tunasafa/mp3-player-enclosure/touchscreen_metal/design_overview.pdf

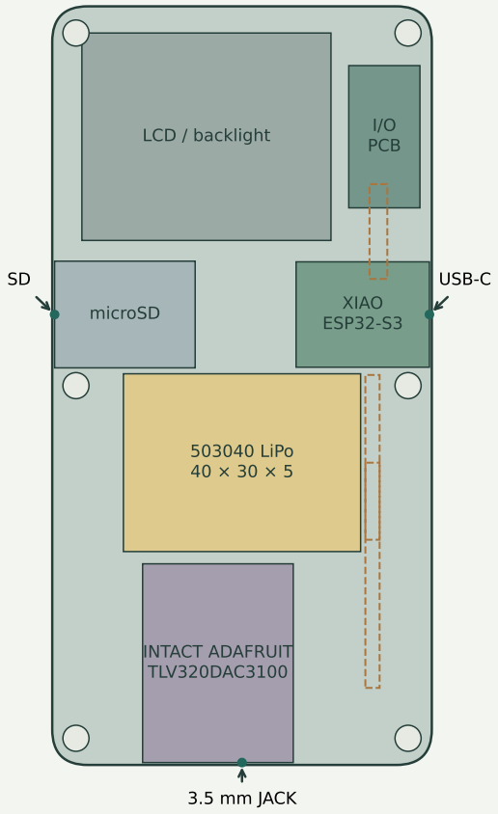
[picture p4: figure]
LCD / backlight; PCB; XIAO ESP32-S3 microSD; 503040 LiPo 40 × 30 × 5; INTACT ADAFRUIT TLV320DAC3100; USB-C; 3.5 mm JACK

LANDSCAPE
296 × 240

## mytunas

64 mm

128 mm

43 × 36 mm outer glass

### 01 / METAL FRONT

### 02 / PACKING — front-coordinate plan

# 8.3 mm aggressive prototype

0.4 mm steel front / 0.15 mm insulation 7.1 mm full Adafruit product height

0.18 mm clearance + 0.07 mm liner

0.4 mm steel rear

# Separate battery bay

5 mm nominal protected pack

2.13 mm to the rear liner

1.7 mm of that reserved clear

# Port alignment

USB right · SD left · headphones bottom

Actual board transforms set USB/jack axes

Blind pockets retain a 1 mm outer lip

# Strict nominal checks

0 assembly collisions

0 reserved-space collisions

Connected, watertight shell / carrier meshes

# Physical fit still required

Panel border and side tails estimated
SD assembly and interface PCB provisional

Unsealed ports; no water/dust rating

### 03 / THICKNESS LIMIT

# mytunas / touch

### T03 / BATTERY ABOVE DAC / BOTTOM JACK / 64 × 128 × 8.3 mm

Metal faces + separate frame. Same coordinates as STEP and viewer; dimensions in millimetres.
Not a fabrication release: qualify plate flatness, deflection, insulation, tolerances and physical component fit.
