tunasafa/mp3-player-enclosure/touchscreen_01/design_overview.pdf

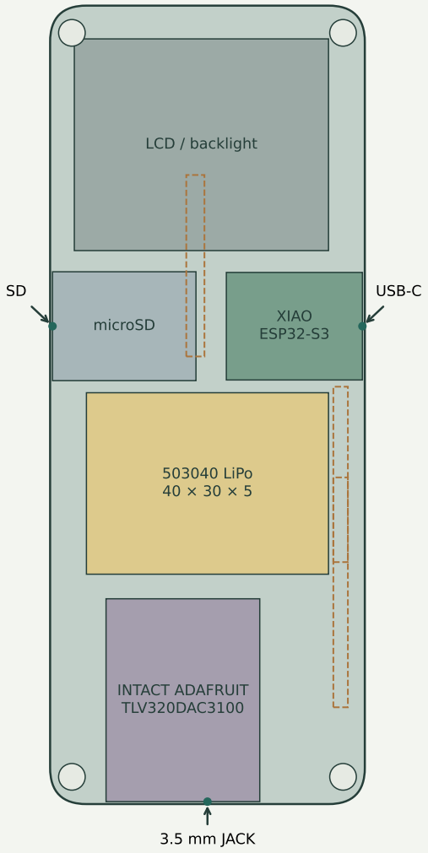
[picture p5: figure]
LCD / backlight; XIAO ESP32-S3 microSD; 503040 LiPo 40 × 30 × 5; INTACT ADAFRUIT TLV320DAC3100; USB-C; 3.5 mm JACK

LANDSCAPE
296 × 240

## mytunas

52 mm

132 mm

43 × 36 mm outer glass

### 01 / FRONT

### 02 / PACKING — front-coordinate plan

# 10.4 mm practical target

1.2 mm front skin
0.6 mm board mounting height

7.1 mm full Adafruit product height

0.3 mm rear clearance

1.2 mm rear skin

# Separate battery bay

5 mm nominal protected pack

2.4 mm to the rear skin

1.7 mm of that reserved clear

# Port alignment

USB right · SD left · headphones bottom

Actual board transforms set USB/jack axes

Blind pockets retain a 1 mm outer lip

# Strict nominal checks

0 assembly collisions

0 reserved-space collisions

Connected, watertight shell / carrier meshes

# Physical fit still required

Panel border and folded ribbons estimated SD assembly and interface PCB provisional

Unsealed ports; no water/dust rating

### 03 / THICKNESS LIMIT

# mytunas / touch

### T02 / BATTERY ABOVE DAC / BOTTOM JACK / 52 × 132 × 10.4 mm

Same parts and coordinates as the STEP assembly and interactive viewer. All dimensions in millimetres. Prototype: sample measurements, flex folding, PCB selection and a physical fit test remain necessary.
