tunasafa/mp3-player-enclosure/revision_04/design_overview.pdf

FRONT SHELL / INSIDE | REAR SHELL / INSIDE

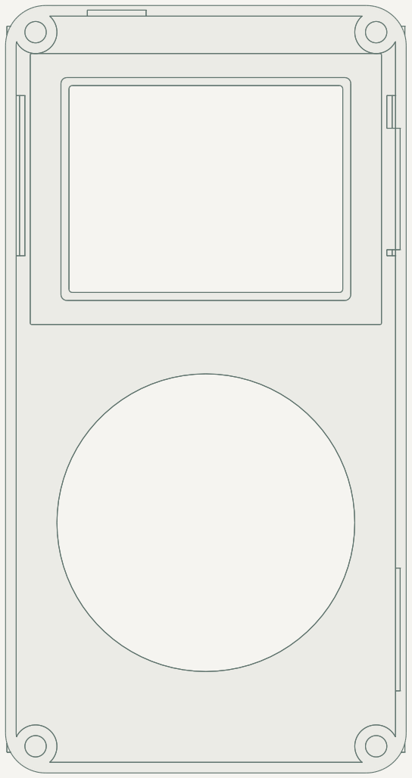
[picture p6: figure]

LCD

Wheel
Battery
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
Assembly Z / mm (front

# → rear)

COMPONENT DEPTH RANGES

# FORM 04 / COMPACT FIT PROTOTYPE

### 115 × 60 × 12.9 mm · repacked with unchanged components · no middle carrier

Lens recess, wheel aperture and local UI pads. Four blind insert bosses; two locating tongues.

Board pads, insertion fences and 503040 battery guides. Viewed through front; same X/Y on both drawings.

Clickwheel adapter to wall: 2.35 mm. Battery to rear skin: 1.7 mm.
DAC to LCD / rear skin: 0.3 / 0.3 mm. These gaps still need real-part verification.

115 x 60 x 12.9 mm; 0.2 mm thinner than 13.1 mm. Battery entirely below LCD; no footprint growth. Flipped upper DAC; 1.0 mm local LCD seat floor.

CAD/mesh checks passed. The component envelopes and connector positions remain provisional.

Print an empty-shell fit set first. Exact wheel/LCD geometry, flex routes, audio mounting and battery sample fit are still required.
