tunasafa/mp3-player-enclosure/touchscreen_02/drawings.pdf

# mytunas / Model 02

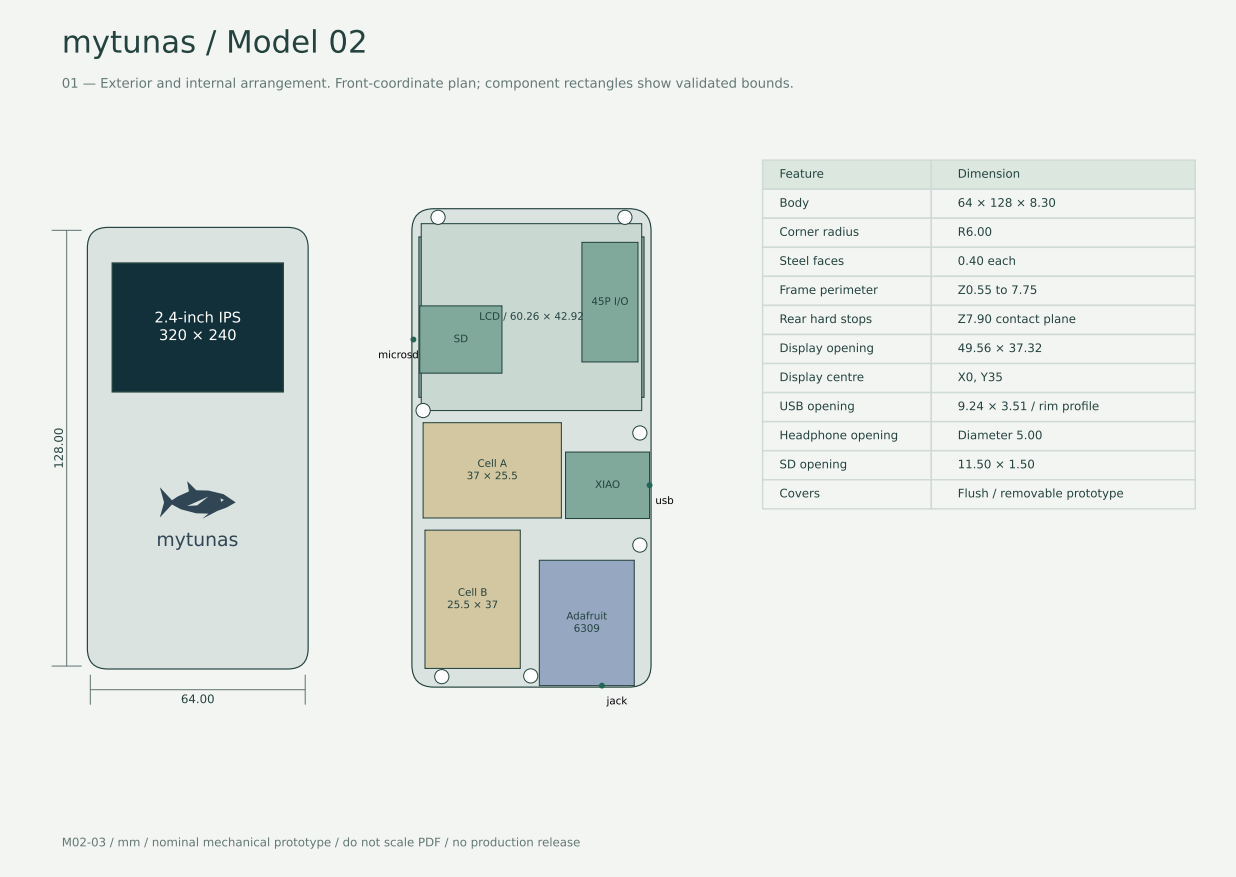
[picture p7: page 1]
2.4-inch IPS 320 × 240; LCD; Cell A 37 × 25.5; Cell B 25.5 × 37; Adafruit 6309; XIAO; usb; jack; microsd; Rear hard stops; Z7.90 contact plane; Headphone opening; Diameter 5.00; SD opening; Covers; Flush / removable prototype

01 — Exterior and internal arrangement. Front-coordinate plan; component rectangles show validated bounds.

Feature | Dimension

Body | 64 × 128 × 8.30

Corner radius | R6.00

Steel faces | 0.40 each

Frame perimeter | Z0.55 to 7.75

Display opening | 49.56 × 37.32

Display centre | X0, Y35

USB opening | 9.24 × 3.51 / rim profile

M02-03 / mm / nominal mechanical prototype / do not scale PDF / no production release

ID | X | Y | Fastener
1 | -25.00 | 61.70 | M1.6 × 5 / CSK

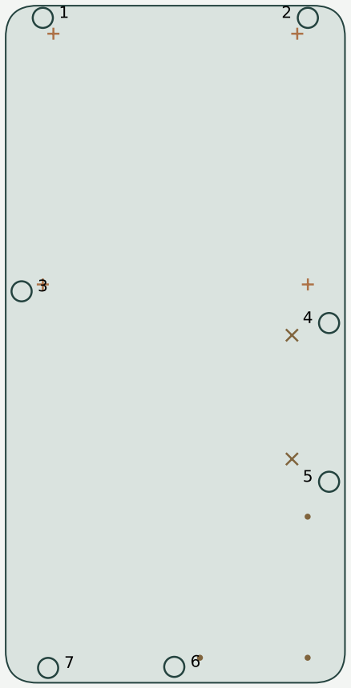
[picture p8: figure]

2 | 25.00 | 61.70 | M1.6 × 5 / CSK
3 | -29.00 | 10.00 | M1.6 × 5 / CSK
4 | 29.00 | 4.00 | M1.6 × 5 / CSK
5 | 29.00 | -26.00 | M1.6 × 5 / CSK
6 | -0.20 | -61.00 | M1.6 × 5 / CSK
7 | -24.00 | -61.20 | M1.6 × 5 / CSK
C1 | -25.00 | 11.30 | M1.4 × 3 / carrier
C2 | 25.00 | 11.30 | M1.4 × 3 / carrier
C3 | -23.00 | 58.70 | M1.4 × 3 / carrier
C4 | 23.00 | 58.70 | M1.4 × 3 / carrier
X1 | 22.00 | -21.70 | M1.4 × 3 / saddle
X2 | 22.00 | 1.70 | M1.4 × 3 / saddle
D1 | 24.96 | -32.60 | M1.4 × 3 / rear column
D2 | 4.64 | -59.27 | M1.4 × 3 / rear column
D3 | 24.96 | -59.27 | M1.4 × 3 / rear column
Mouth centre | X | Y | Z
usb | 31.6000 | -9.9927 | 3.6050
jack | 18.8592 | -63.6000 | 4.4225
microsd | -31.6000 | 29.0000 | 6.4000

# Hole and port coordinates

02 — Datum: body centre X0/Y0; front exterior Z0. All dimensions in millimetres.

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
### Z / mm

0.00–0.40

Steel

0.40–0.55

Insulation

0.55–7.65

Published DAC max

7.65–7.83

Free 0.18

7.83–7.90

Liner

7.90–8.30

Steel

## DAC

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
### Z / mm

0.00–0.40

Steel

0.40–0.70

Adhesive

0.70–5.90

Pack max 5.20

5.90–7.60

Expansion 1.70

7.60–7.83

Free 0.23

7.83–7.90

Liner

7.90–8.30

Steel

## Battery

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
### Z / mm

0.00–0.40

Bezel

0.40–0.55

Bond

0.55–4.30

Touch + LCD 3.75

4.30–4.35

Cushion

4.35–4.55

Carrier

4.55–4.85

SD adhesive

4.85–7.45

SD max

7.45–7.83

Free 0.38

7.83–7.90

Liner

7.90–8.30

Steel

## LCD + SD

# Depth sections and reserves

03 — Layer values are nominal allocations. Full published DAC height is retained.

Part / check | Specification | Process note
Frame | PA12 / 13 metal threaded inserts | Use BEFORE_HEAT_INSERTS geometry
Front / rear | 0.40 mm satin polished stainless | 0.03 mm original vector engravings
Carrier | 0.20 web / four 0.30 mm welded blades | Weld in flat fixture; inspect distortion
Case threads | 7 × PEM MSIB-M1.6-300 | Pilot 2.15 / depth 3.77 minimum
Internal threads | 6 × PEM MSIB-M1.4-150 | Pilot 2.15 / depth 2.27 minimum
XIAO saddle | 0.40 steel / 0.30 shield cushion | Two M1.4 × 3 screws; qualify shield load
DAC retention | 3 steel columns / insulated seats | Three rear M1.4 × 3 CSK screws
Ports | Actual USB rim + 0.15 radial gap | Positive clearance; optional covers
Release gate | 0.18 mm DAC clearance is tight | Tolerance stack and physical cycle tests

# Manufacturing and assembly checkpoints

04 — STEP defines 3D geometry. DXF profiles are for the named sheet layers only.

Part | W × L × H | Minimum X, Y, Z
case_insert_1 | 2.50 × 2.50 × 3.00 | -26.25, 60.45, 4.50
case_insert_2 | 2.50 × 2.50 × 3.00 | 23.75, 60.45, 4.50
case_insert_3 | 2.50 × 2.50 × 3.00 | -30.25, 8.75, 4.50
case_insert_4 | 2.50 × 2.50 × 3.00 | 27.75, 2.75, 4.50
case_insert_5 | 2.50 × 2.50 × 3.00 | 27.75, -27.25, 4.50
case_insert_6 | 2.50 × 2.50 × 3.00 | -1.45, -62.25, 4.50
case_insert_7 | 2.50 × 2.50 × 3.00 | -25.25, -62.45, 4.50
carrier_insert_1 | 2.50 × 2.50 × 1.50 | -26.25, 10.05, 2.85
carrier_insert_2 | 2.50 × 2.50 × 1.50 | 23.75, 10.05, 2.85
carrier_insert_3 | 2.50 × 2.50 × 1.50 | -24.25, 57.45, 2.85
carrier_insert_4 | 2.50 × 2.50 × 1.50 | 21.75, 57.45, 2.85
xiao_clamp_insert_1 | 2.50 × 2.50 × 1.50 | 20.75, -22.95, 2.80
xiao_clamp_insert_2 | 2.50 × 2.50 × 1.50 | 20.75, 0.45, 2.80
midframe | 64.01 × 128.01 × 7.35 | -32.00, -64.00, 0.55
front_bezel | 64.01 × 128.01 × 0.41 | -32.00, -64.00, -0.00
rear_shell | 64.01 × 128.01 × 0.41 | -32.00, -64.00, 7.90
front_bond | 64.01 × 128.01 × 0.16 | -32.00, -64.00, 0.40
rear_gasket | 64.01 × 128.01 × 0.16 | -32.00, -64.00, 7.75
touch_glass | 59.96 × 42.62 × 1.25 | -29.98, 13.69, 0.55
lcd | 60.26 × 42.92 × 2.50 | -30.13, 13.54, 1.80

# Part measurement schedule

05 — Bounding dimensions and assembly position; holes and contours are defined by STEP.

Part | W × L × H | Minimum X, Y, Z
display_adhesive | 59.66 × 42.32 × 0.15 | -29.83, 13.84, 0.40
display_carrier | 59.00 × 50.00 × 1.45 | -29.50, 10.00, 4.35
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
usb_cover | 0.45 × 12.60 × 6.00 | 31.55, -16.29, 0.60
sd_cover | 0.45 × 13.20 × 2.60 | -32.00, 22.40, 5.10
jack_cover | 6.50 × 0.45 × 6.50 | 15.61, -64.00, 1.17

08 — Bounding dimensions and assembly position; holes and contours are defined by STEP.
