tunasafa/mp3-player-enclosure/revision_04/studies/dac_orientation/comparison.pdf

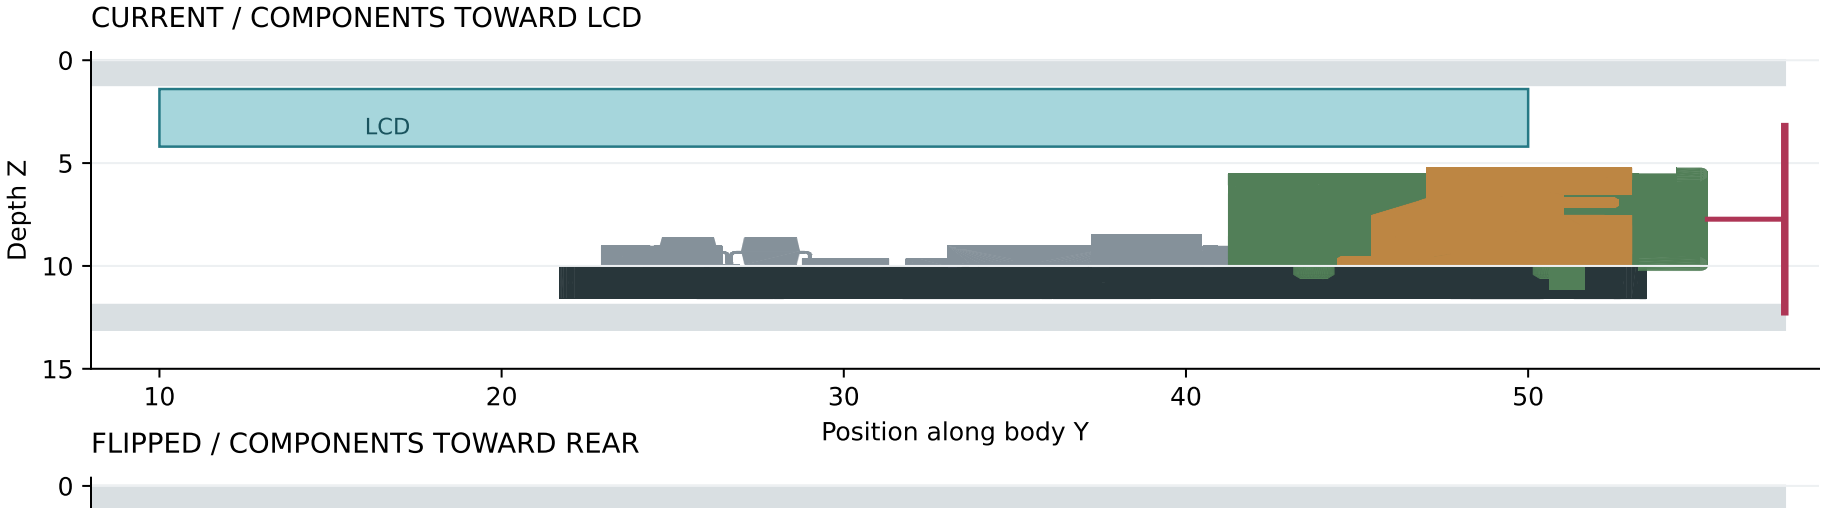
[picture p9: figure]
Position along body Y; Depth Z; LCD; CURRENT / COMPONENTS TOWARD LCD; FLIPPED / COMPONENTS TOWARD REAR

10 | 20 | 30 | 40 | 50
| | Position along body Y

5

10

15

Depth Z

LCD

10 | 20 | 30 | 40 | 50
| | Position along body Y

0

5

10

15

Depth Z

LCD

CONDITIONAL / NOMINAL CAD HEIGHT

# mytunas / DAC orientation study

Same Adafruit 6309 board, including both connectors. Dimensions in mm.

Case: 13.1
Jack axis Z: 7.728

Rear aperture ligament: 0.872

Published board stack: 7.1 Envelope rear gap: 0.3

Existing printable design

Case: 13.1
Jack axis Z: 8.372

Rear aperture ligament: 0.228

Published board stack unchanged

Hole and mounts must move
Rear aperture edge becomes thin

Case: 12.4
Jack axis Z: 7.000

Rear aperture ligament: 0.900 CAD-only fit target

7.1 published height NOT cleared

Battery rear space: 1.0

## WHY SIDEWAYS DOES NOT AUTOMATICALLY SAVE DEPTH

Jack housing reaches 14.0 into the board. Free space beside the centered LCD is only 2.4.

The jack and speaker socket still sit over the LCD when rotated to a side port.

Moving them entirely beyond the LCD trades thickness for a larger face footprint.

Side projections of manufacturer CAD, not cross-sections. Gray: shells. Cyan: LCD. Green: jack. Ochre: speaker socket.

Study only: nominal CAD is not a maximum-part drawing. No new print release or electrical qualification.
