tunasafa/mp3-player-enclosure/touchscreen_01/designs/T01_concept/README_SUPERSEDED.md

# Superseded — do not print

These T01 files contain known component and support intersections. The old validation bypass was removed. They are retained only as historical output.

Use the current [T02 bottom-jack exports](../T02_bottom_jack/) and [validated interactive preview](../../preview.html).
