tunasafa/mp3-player-enclosure/revision_04/internal_layout.png

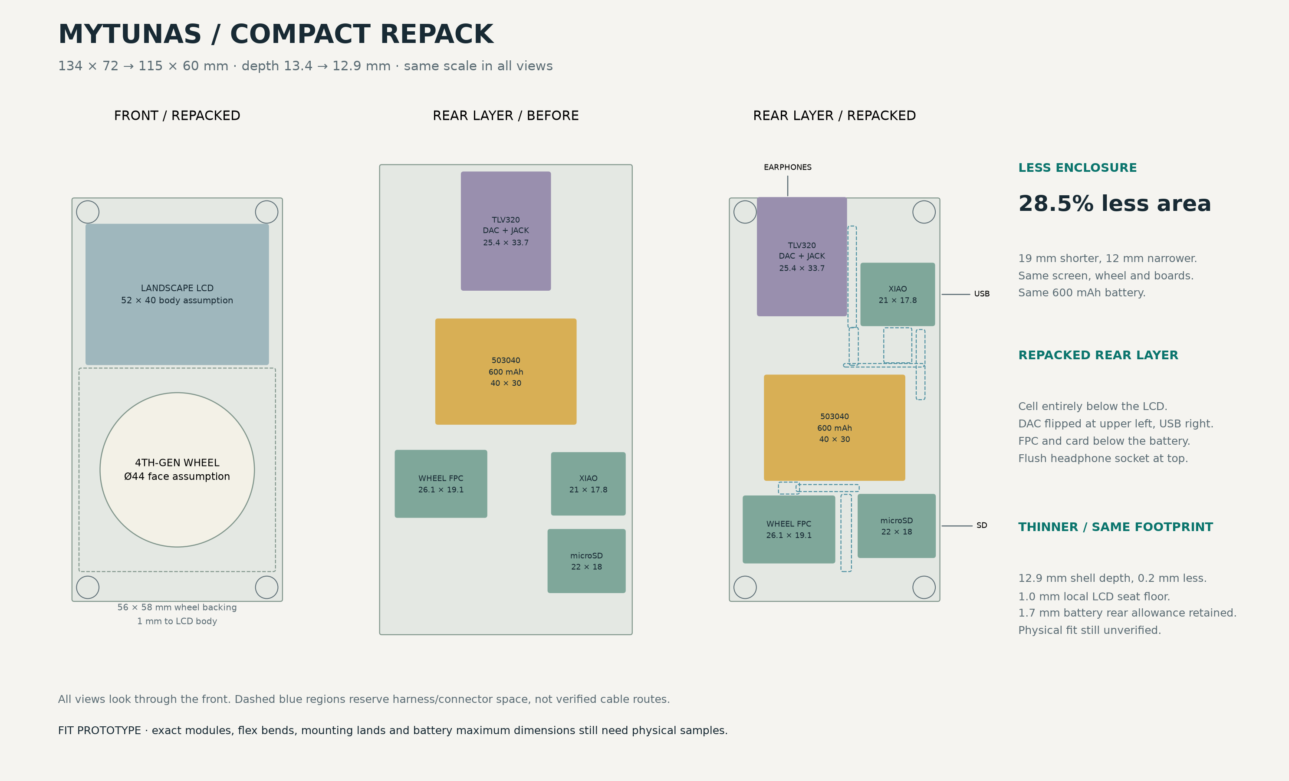
revision_04/internal_layout.png
