tunasafa/mp3-player-enclosure/revision_04/preview_bottom_check.png

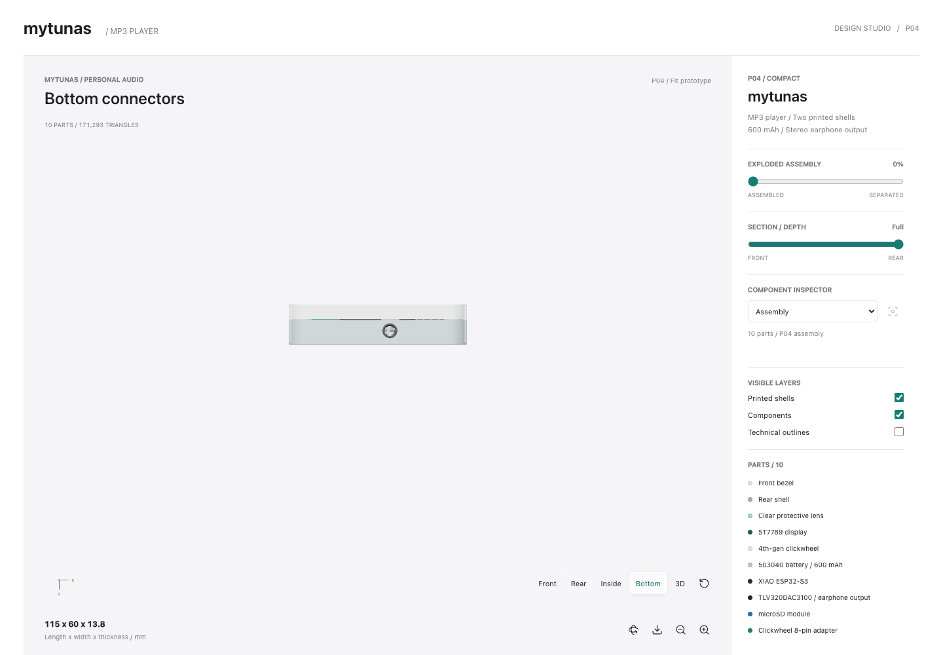
revision_04/preview_bottom_check.png
