tunasafa/mp3-player-enclosure/revision_04/preview_mobile_inside_check.png

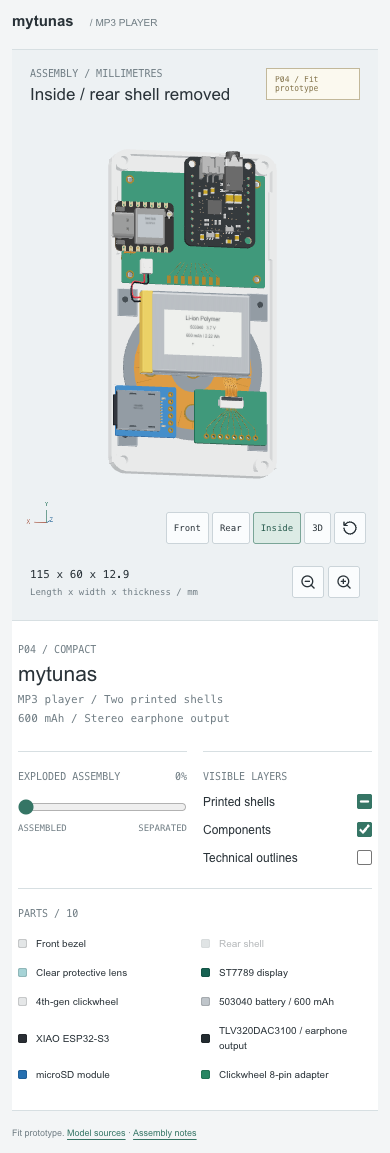
revision_04/preview_mobile_inside_check.png
