tunasafa/mp3-player-enclosure/revision_04/preview_section_check.png

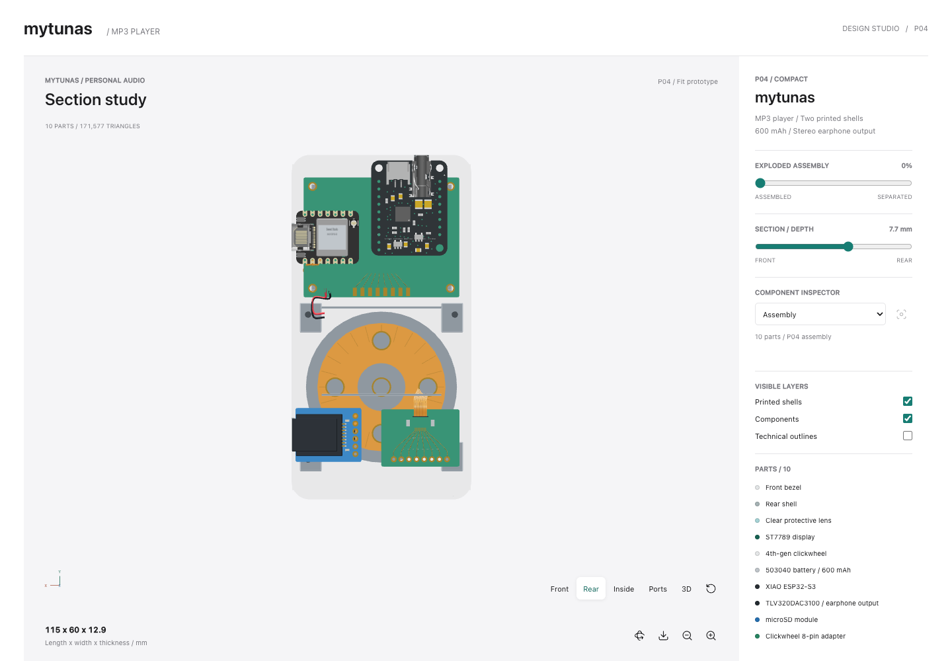
revision_04/preview_section_check.png
