tunasafa/mp3-player-enclosure/revision_04/preview_small_mobile_rear_check.png

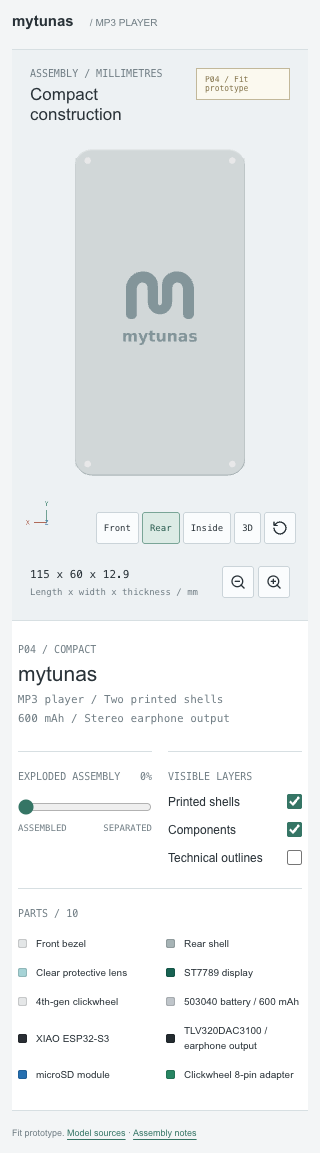
revision_04/preview_small_mobile_rear_check.png
