tunasafa/mp3-player-enclosure/touchscreen_01/design_overview.png

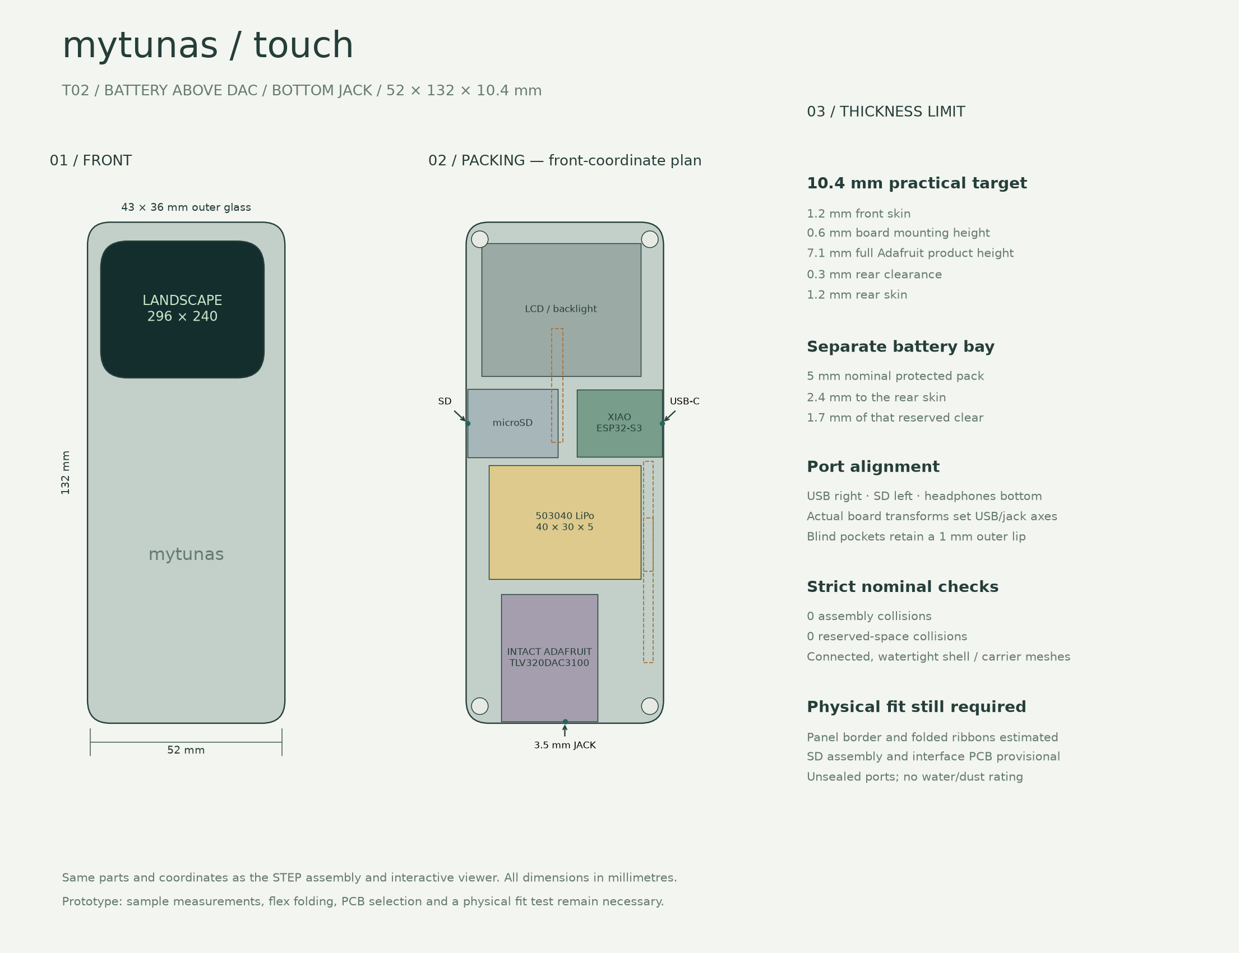
touchscreen_01/design_overview.png
