tunasafa/mp3-player-enclosure/touchscreen_01/preview_back.png

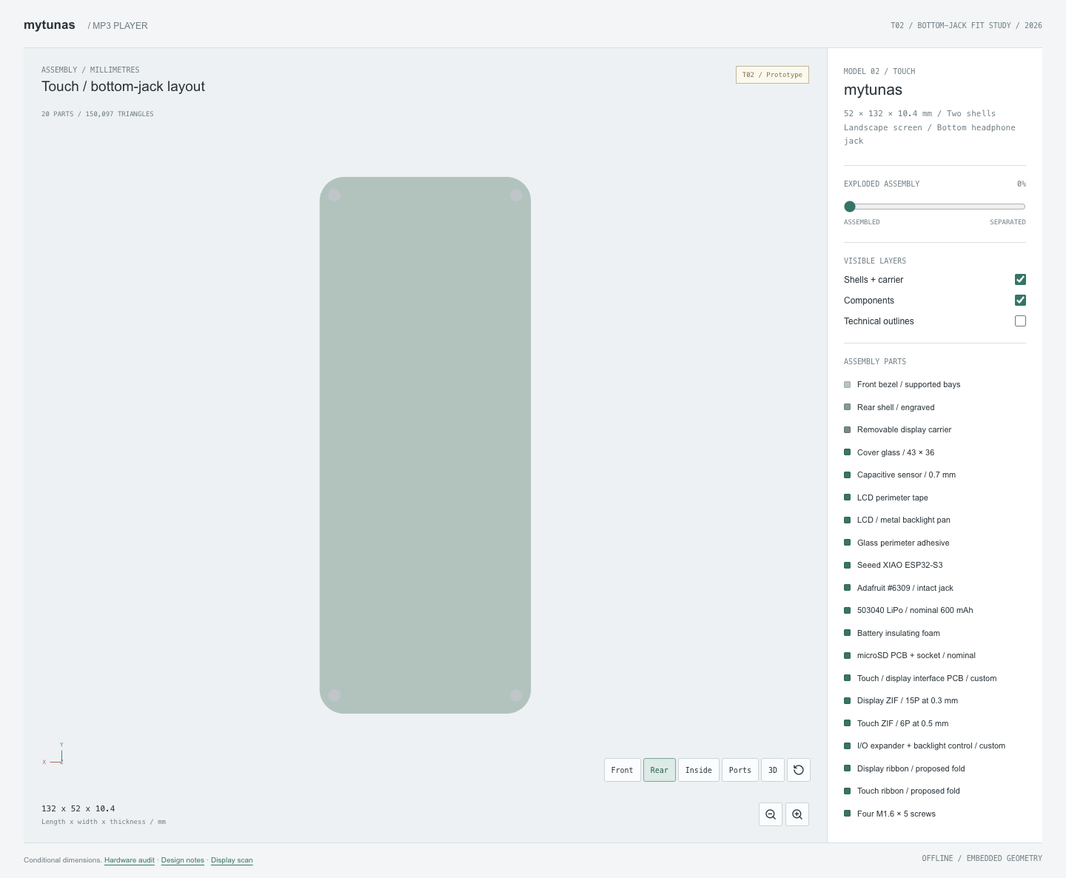
touchscreen_01/preview_back.png
