tunasafa/mp3-player-enclosure/touchscreen_01/preview_exploded.png

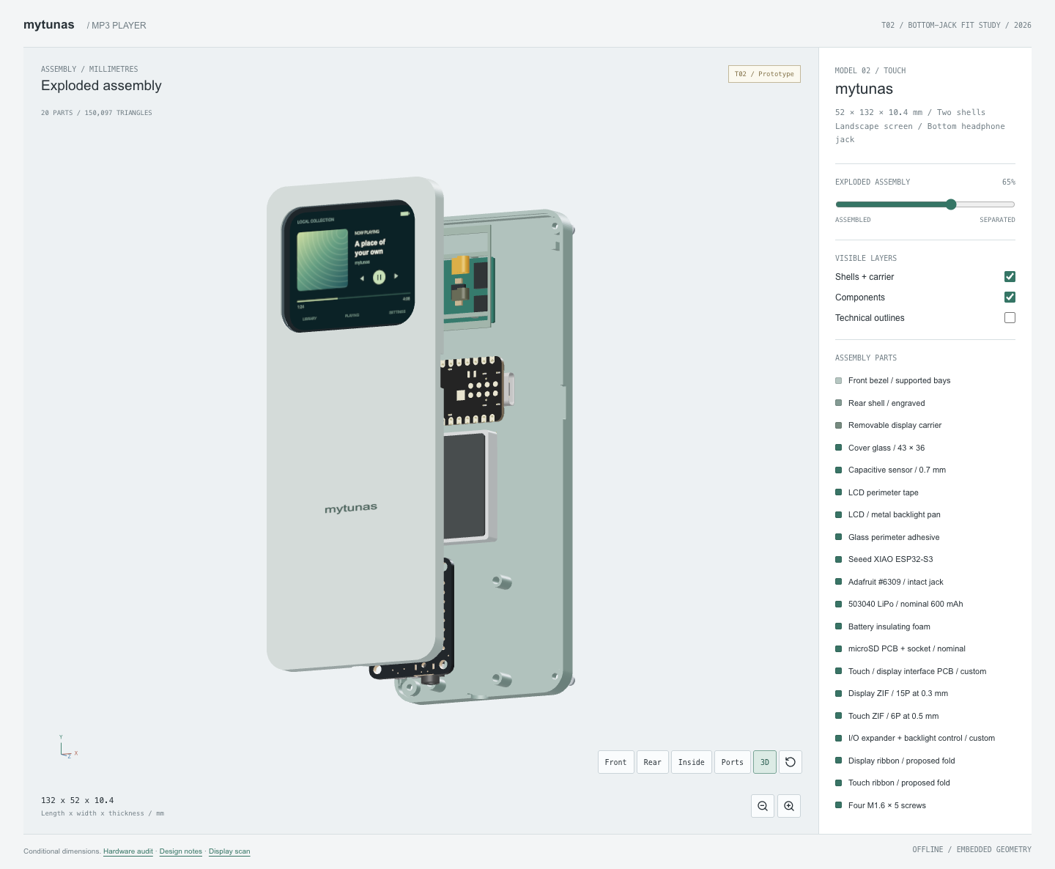
touchscreen_01/preview_exploded.png
