tunasafa/mp3-player-enclosure/touchscreen_01/preview_exploded_full.png

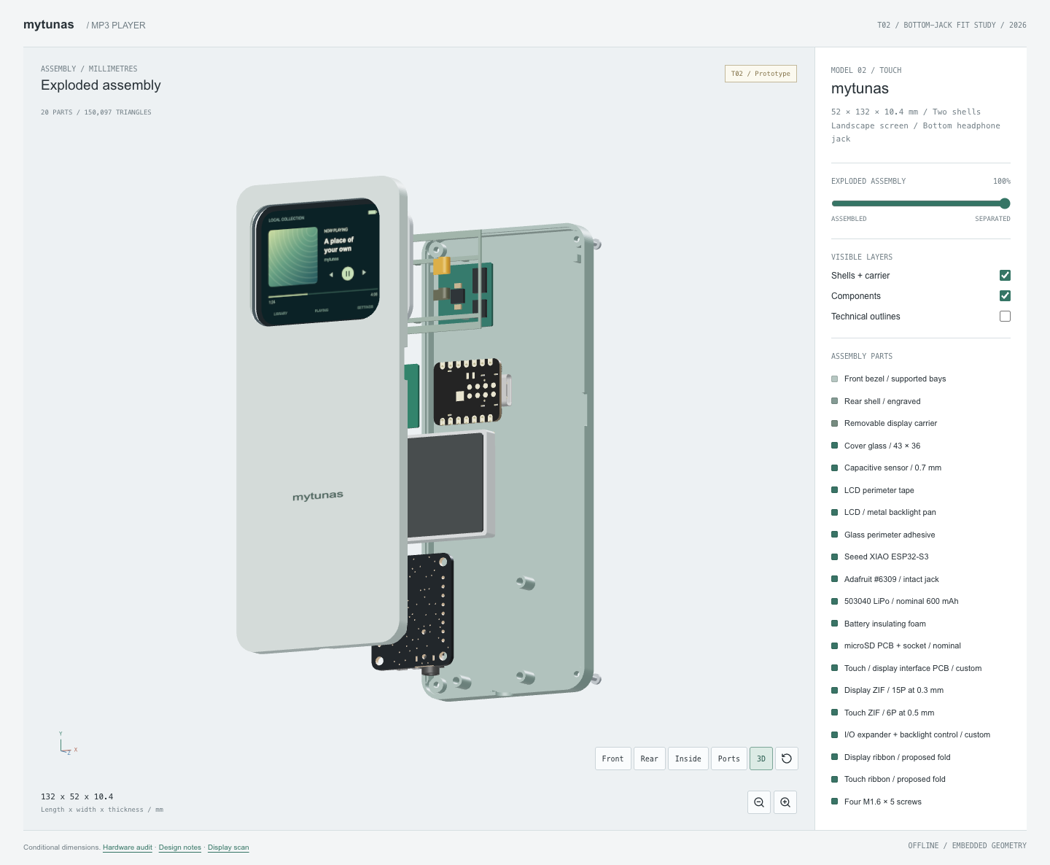
touchscreen_01/preview_exploded_full.png
