tunasafa/mp3-player-enclosure/touchscreen_01/preview_mobile.png

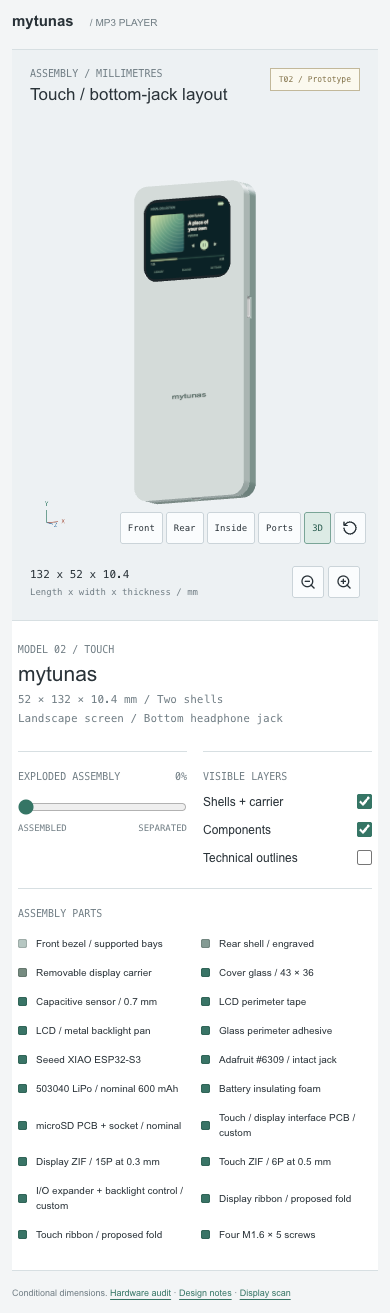
touchscreen_01/preview_mobile.png
