tunasafa/mp3-player-enclosure/touchscreen_01/preview_mobile_inside.png

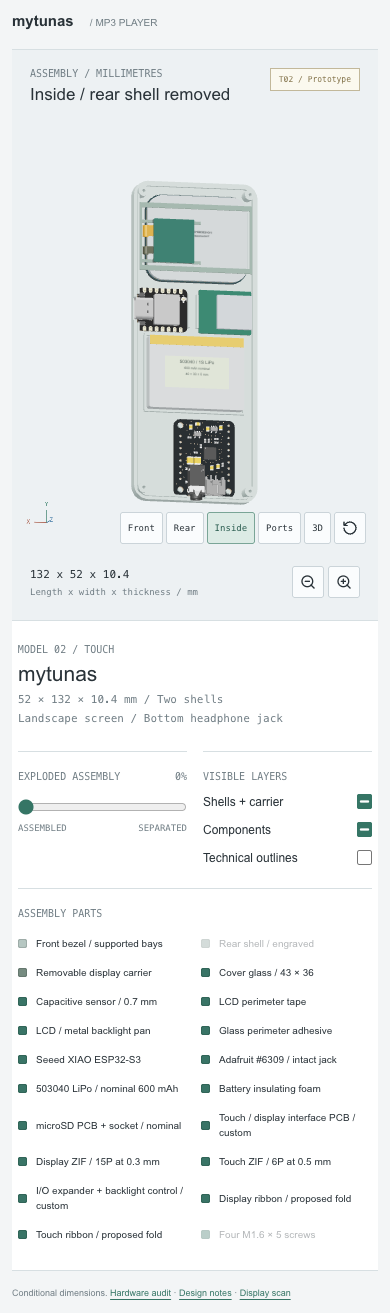
touchscreen_01/preview_mobile_inside.png
