tunasafa/mp3-player-enclosure/touchscreen_01/preview_ports.png

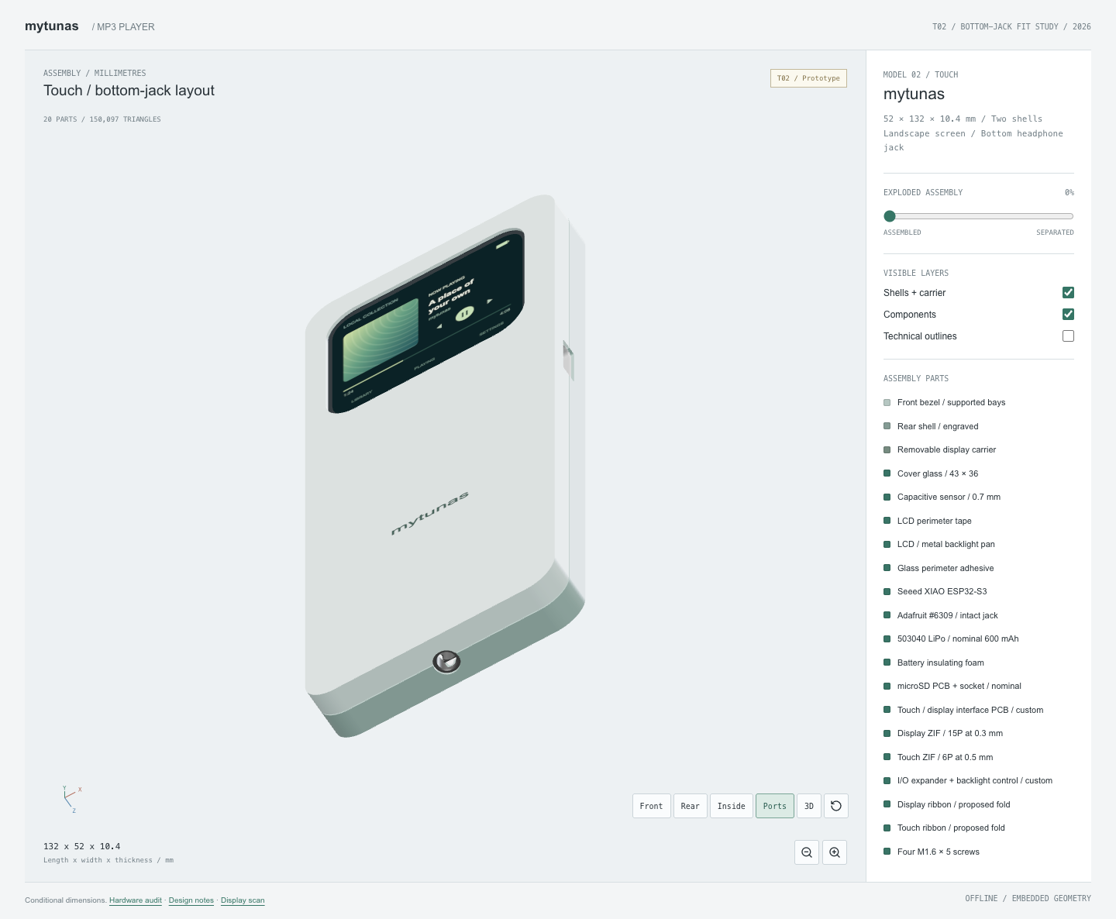
touchscreen_01/preview_ports.png
