tunasafa/mp3-player-enclosure/touchscreen_01/scan/inspection.png

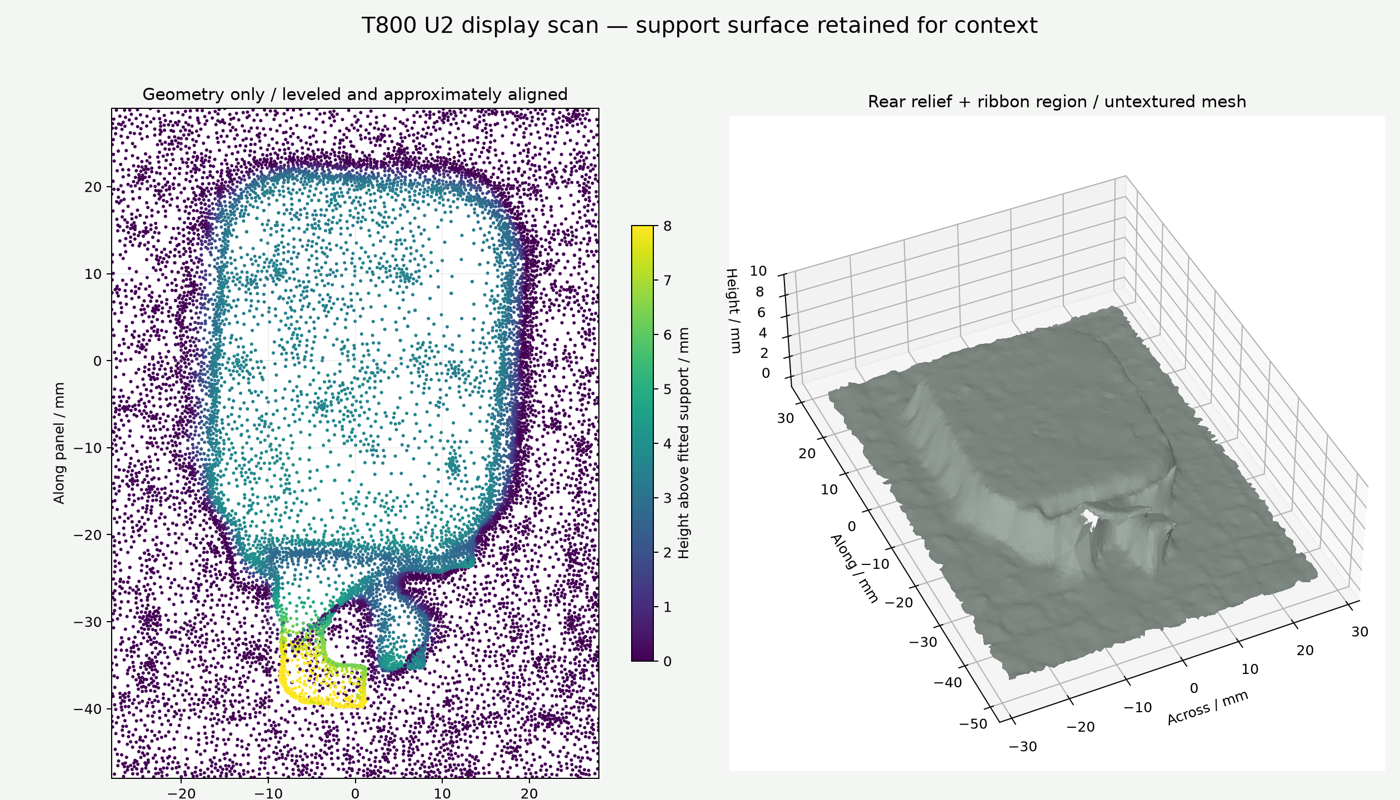
touchscreen_01/scan/inspection.png
