tunasafa/mp3-player-enclosure/touchscreen_01/scan/newtouchscreenchart.png

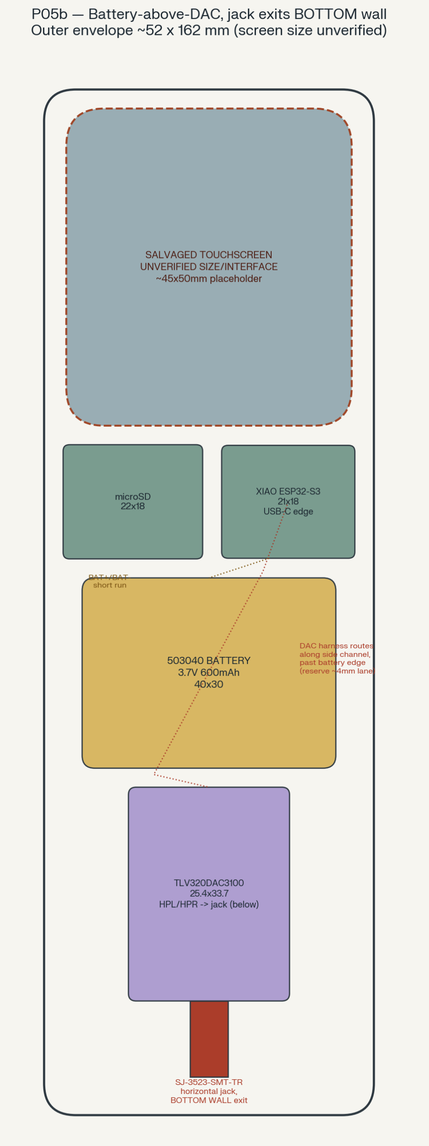
touchscreen_01/scan/newtouchscreenchart.png
