tunasafa/mp3-player-enclosure/touchscreen_01/scan/raw_inspection.png

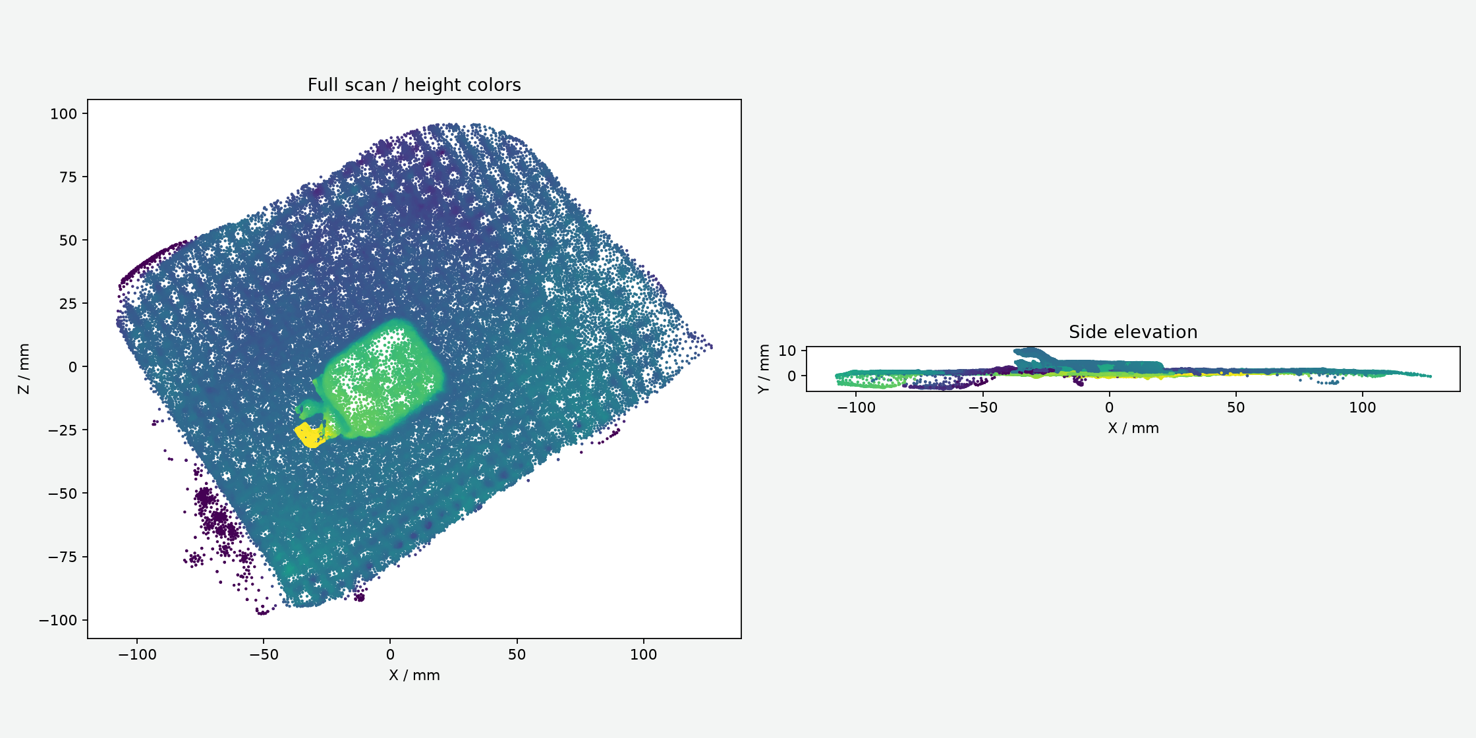
touchscreen_01/scan/raw_inspection.png
