tunasafa/mp3-player-enclosure/touchscreen_02/depth_sections.png

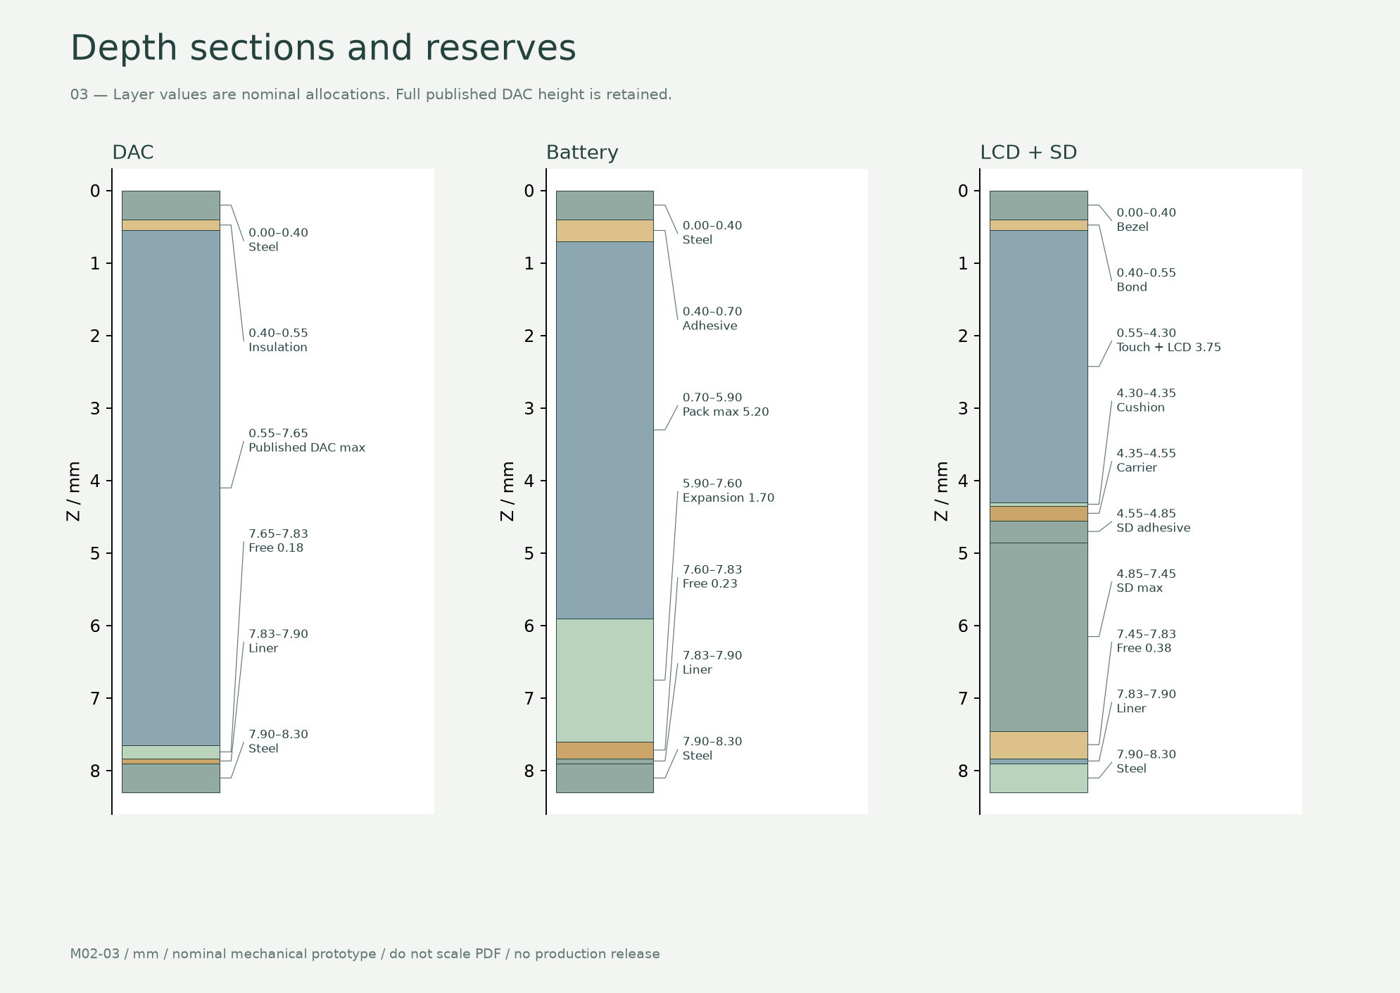
touchscreen_02/depth_sections.png
