tunasafa/mp3-player-enclosure/touchscreen_02/pla_fit/preview_mobile.png

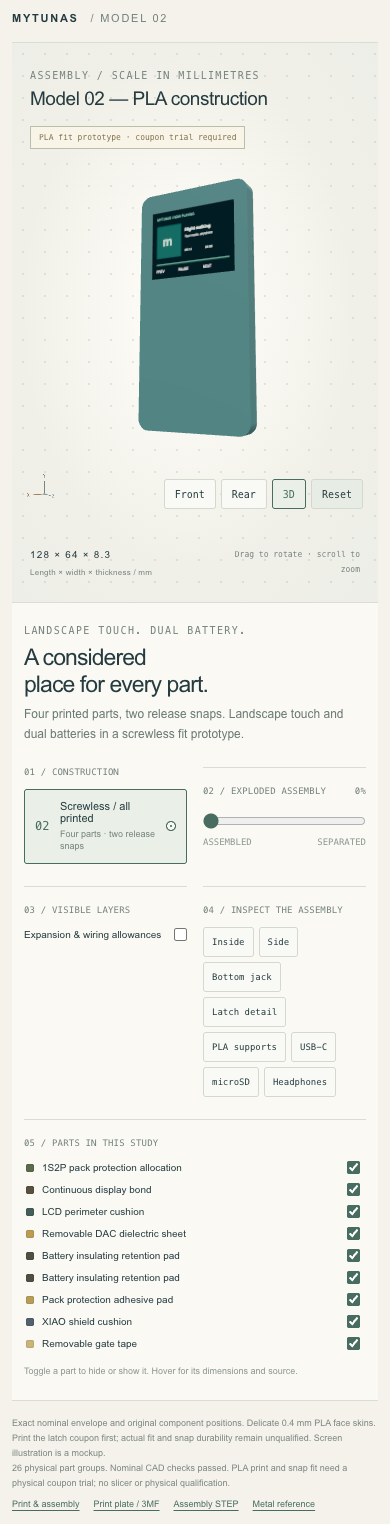
touchscreen_02/pla_fit/preview_mobile.png
