tunasafa/mp3-player-enclosure/touchscreen_02/preview_bottom.png

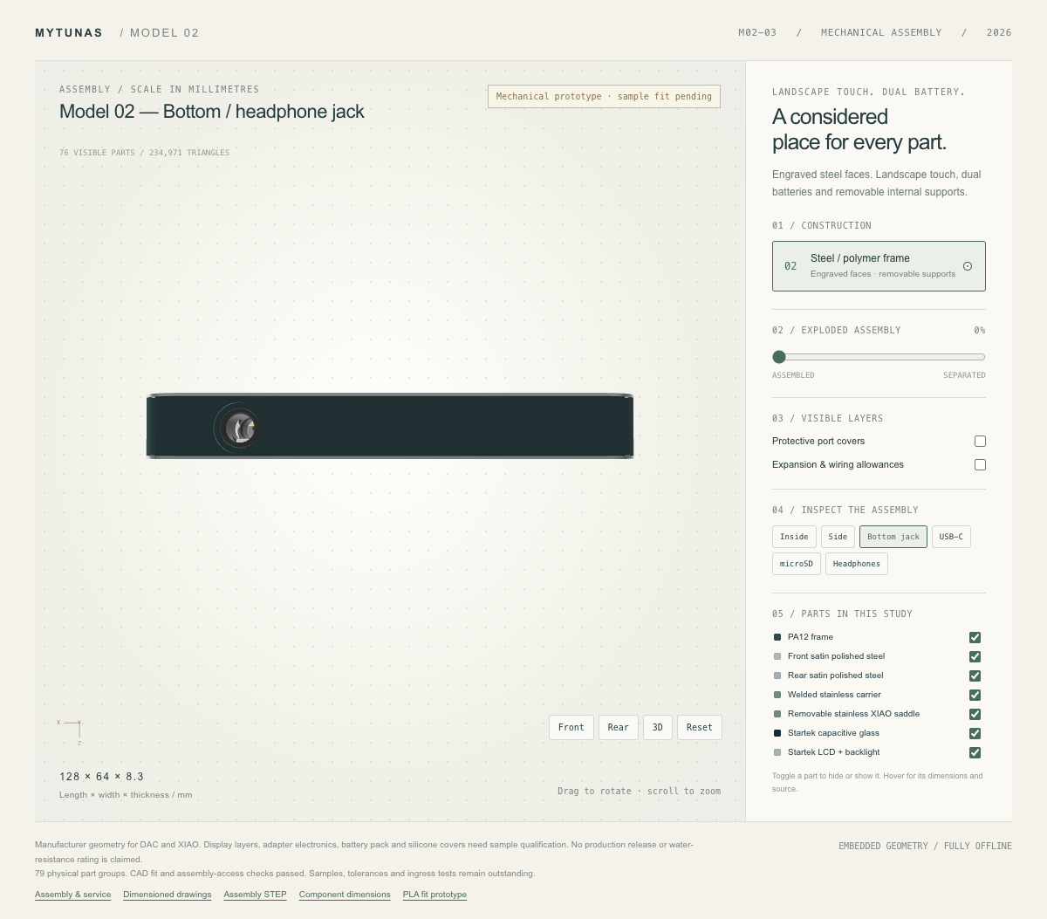
touchscreen_02/preview_bottom.png
