tunasafa/mp3-player-enclosure/touchscreen_02/preview_mobile.png

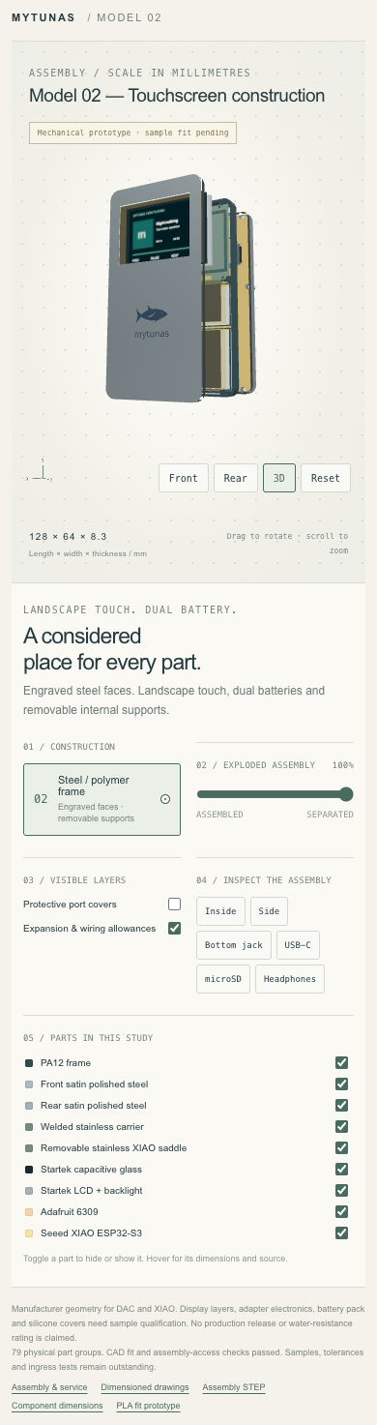
touchscreen_02/preview_mobile.png
