tunasafa/mp3-player-enclosure/touchscreen_02/preview_mobile_inside.png

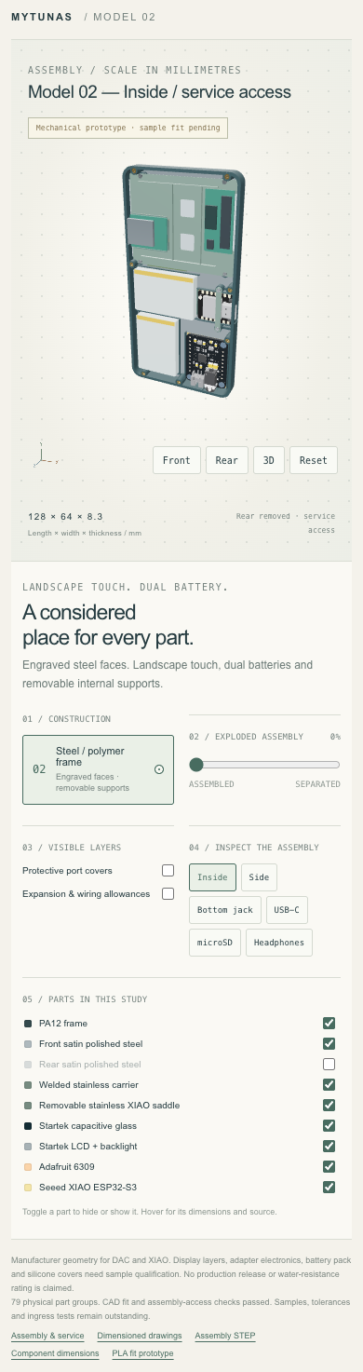
touchscreen_02/preview_mobile_inside.png
