tunasafa/mp3-player-enclosure/touchscreen_02/preview_port_jack.png

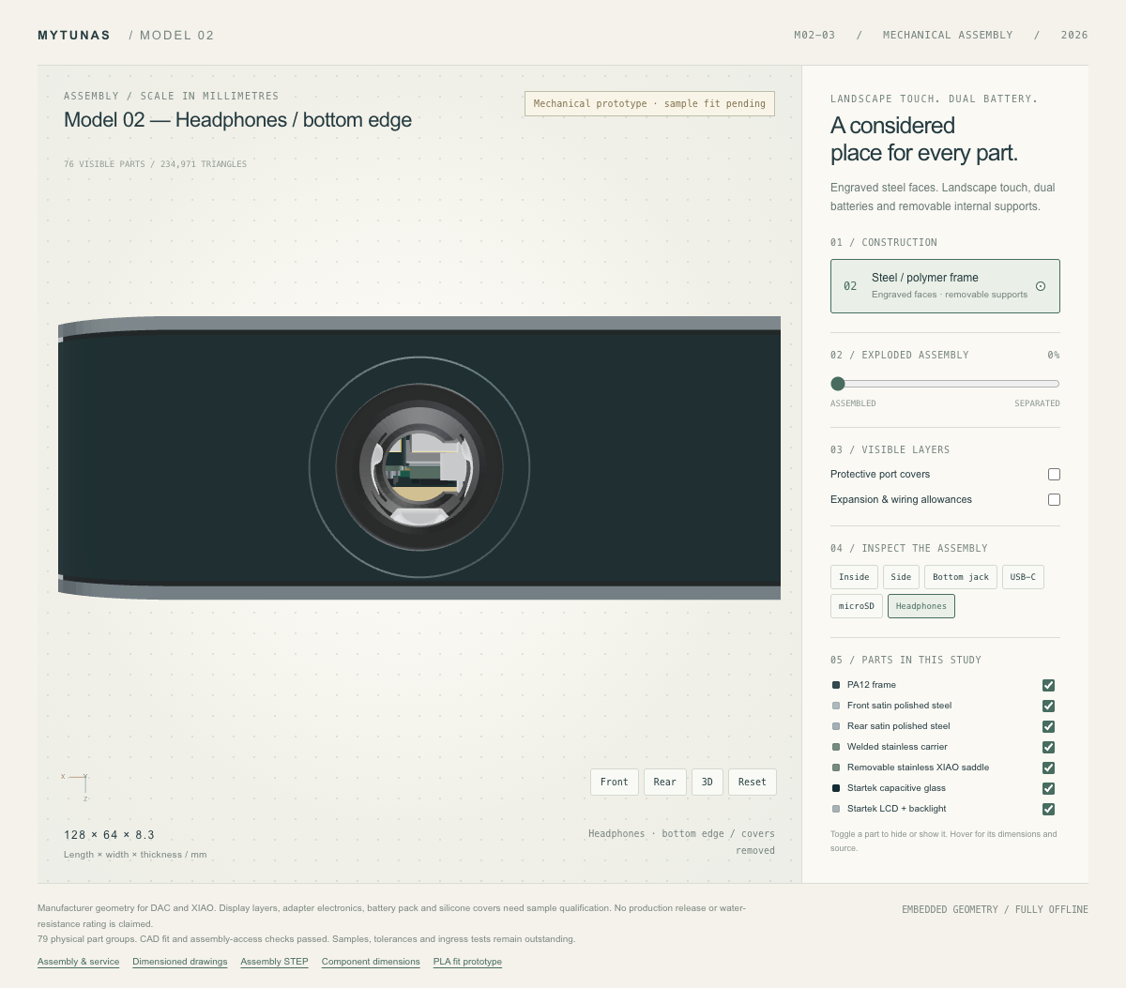
touchscreen_02/preview_port_jack.png
