tunasafa/mp3-player-enclosure/touchscreen_02/preview_side.png

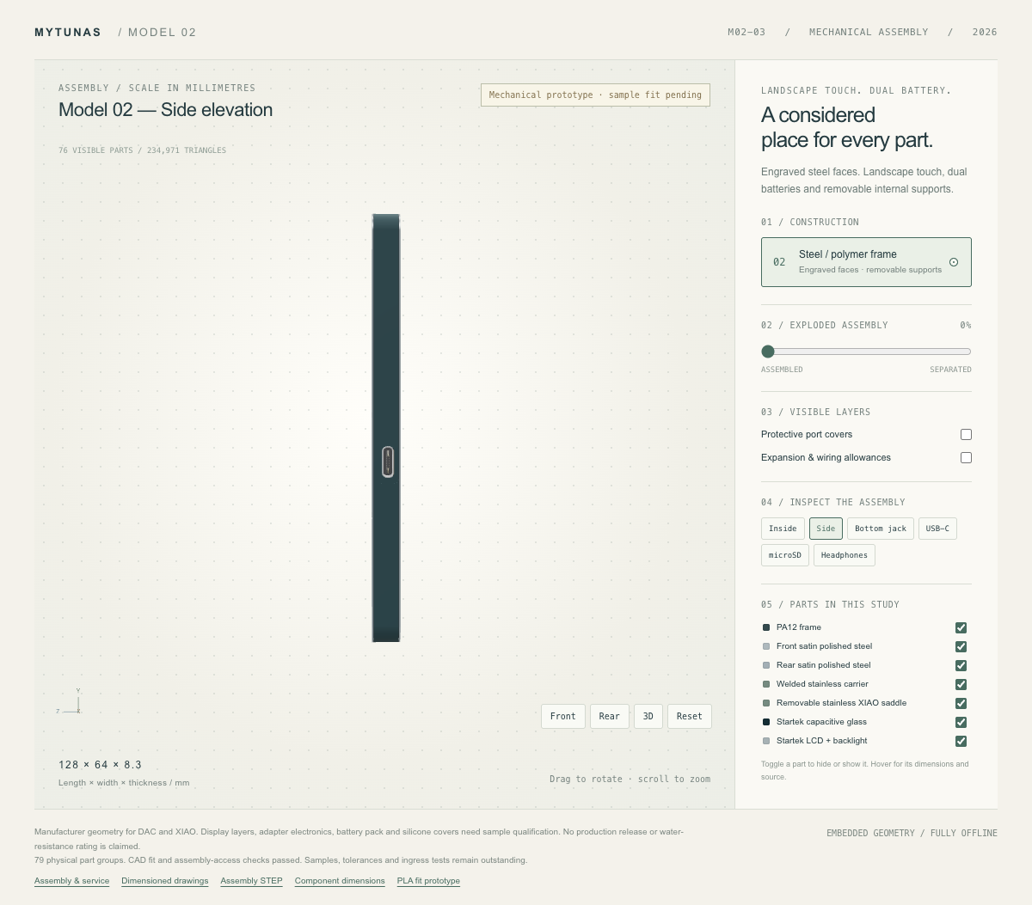
touchscreen_02/preview_side.png
