tunasafa/mp3-player-enclosure/touchscreen_metal/preview_back.png

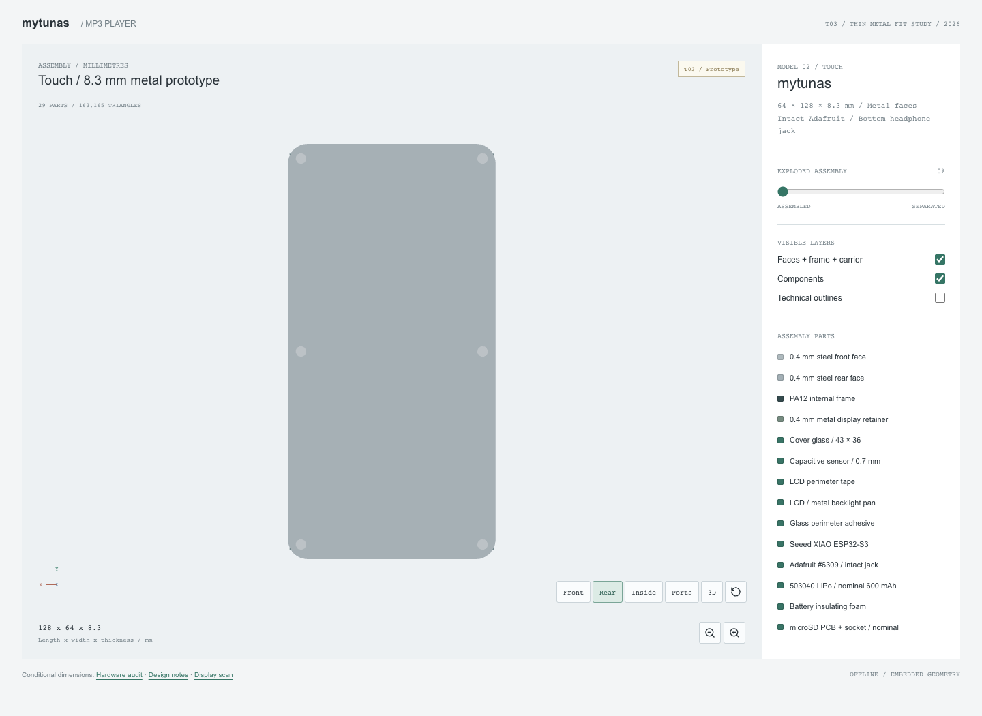
touchscreen_metal/preview_back.png
