tunasafa/mp3-player-enclosure/touchscreen_metal/preview_exploded.png

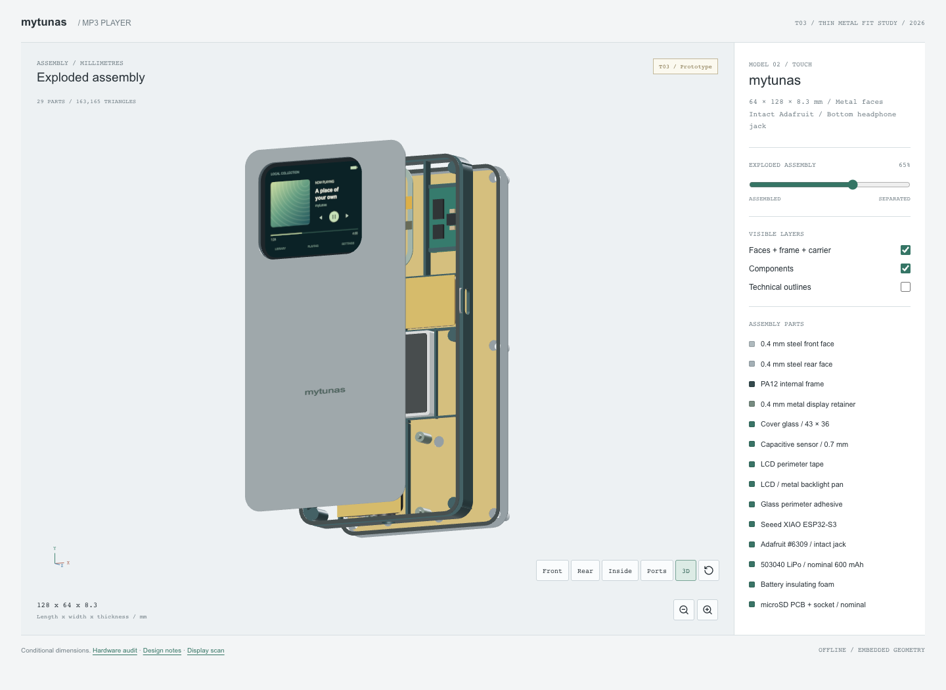
touchscreen_metal/preview_exploded.png
