tunasafa/mp3-player-enclosure/touchscreen_metal/preview_exploded_full.png

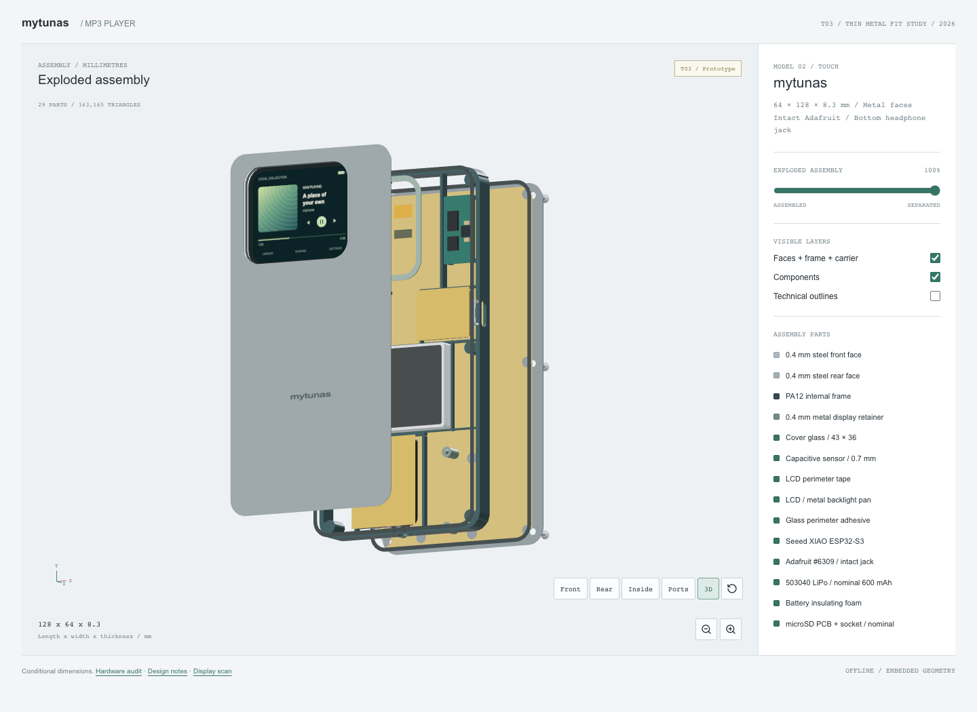
touchscreen_metal/preview_exploded_full.png
