tunasafa/mp3-player-enclosure/touchscreen_metal/preview_inside.png

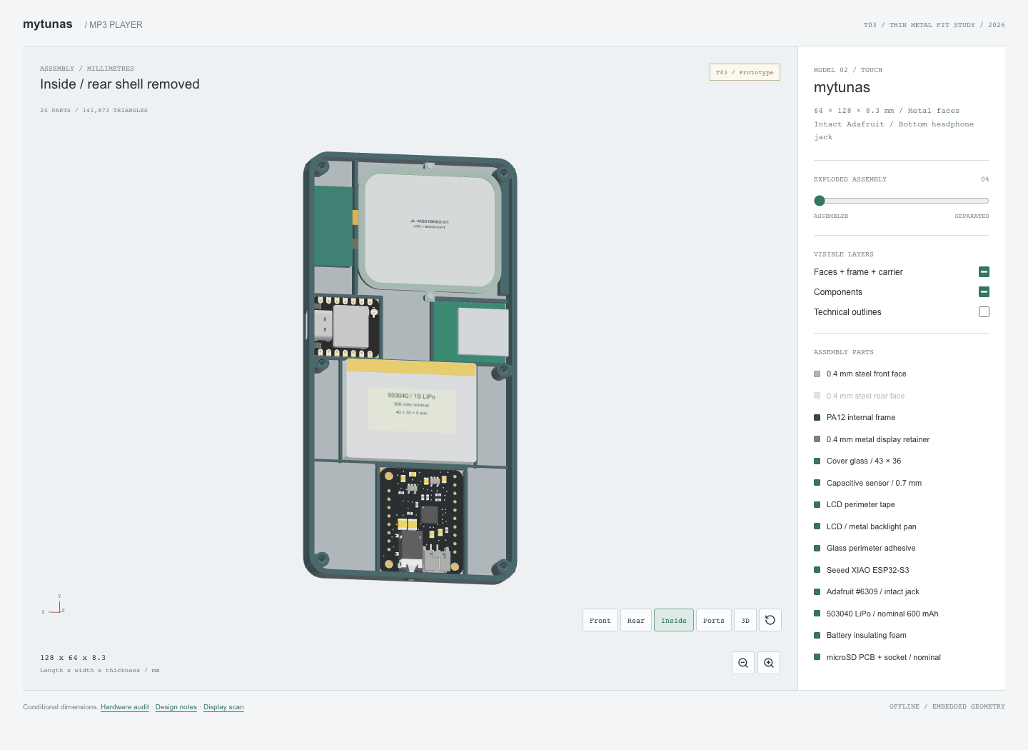
touchscreen_metal/preview_inside.png
