tunasafa/mp3-player-enclosure/touchscreen_metal/preview_mobile.png

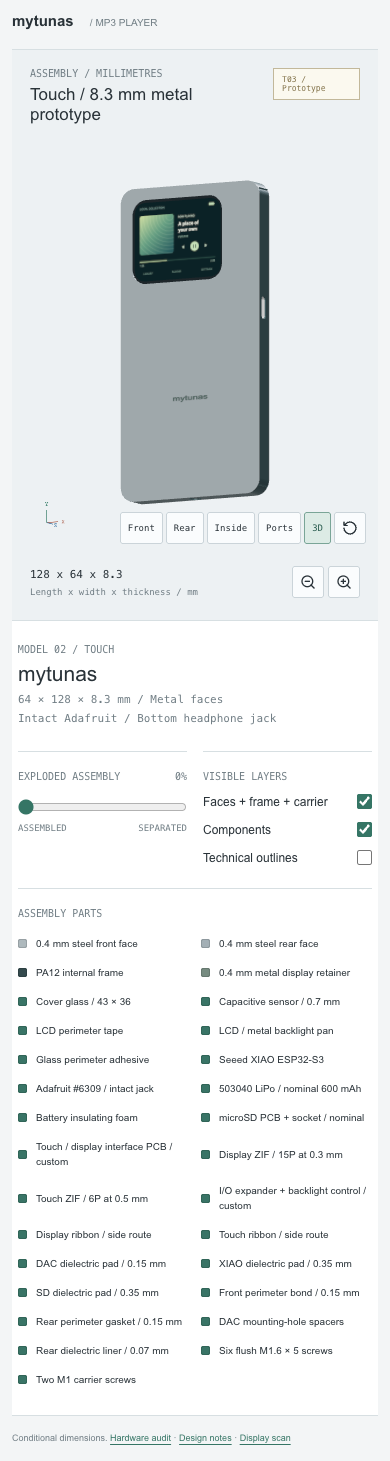
touchscreen_metal/preview_mobile.png
