tunasafa/mp3-player-enclosure/touchscreen_metal/preview_mobile_inside.png

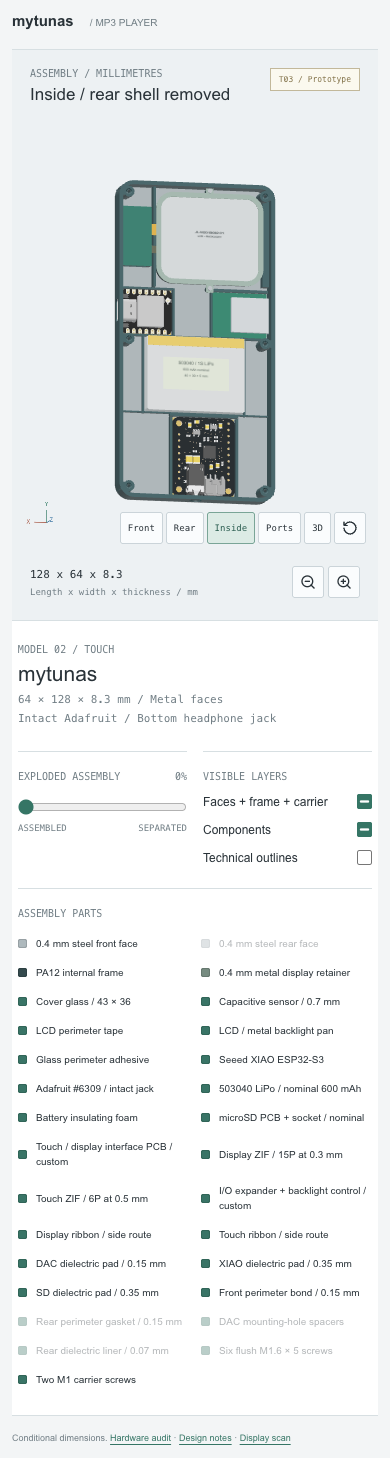
touchscreen_metal/preview_mobile_inside.png
