tunasafa/mp3-player-enclosure/touchscreen_metal/preview_ports.png

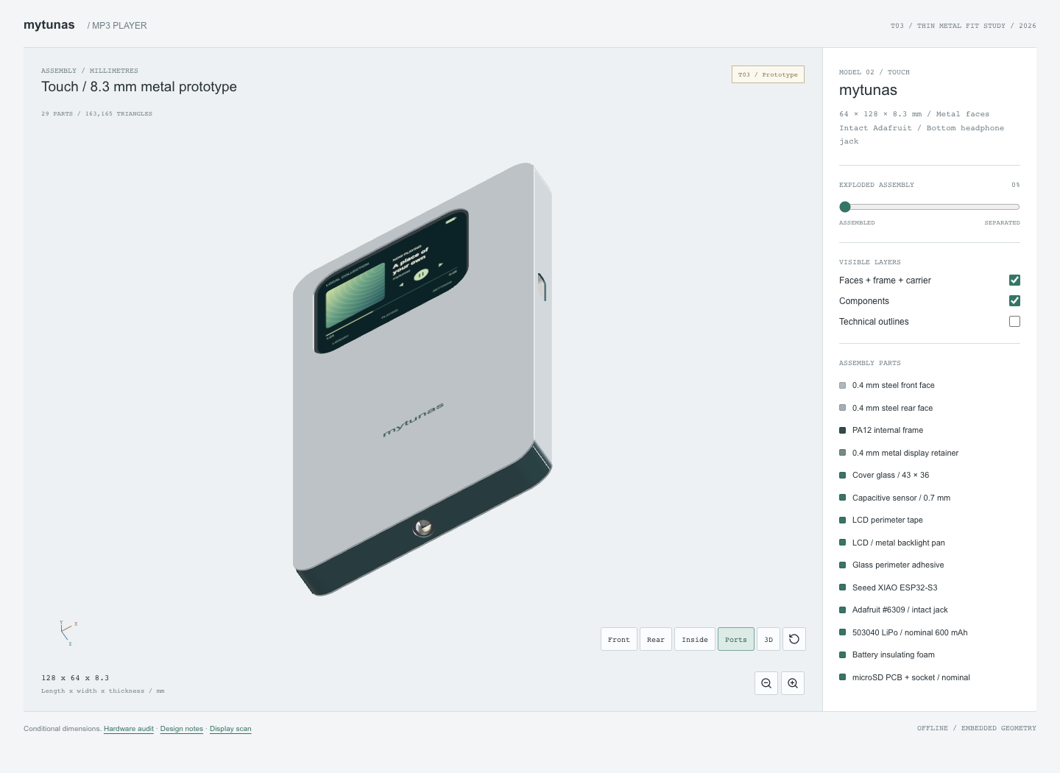
touchscreen_metal/preview_ports.png
