tunasafa/mp3-player-enclosure/touchscreen_metal/scan_preview_check.png

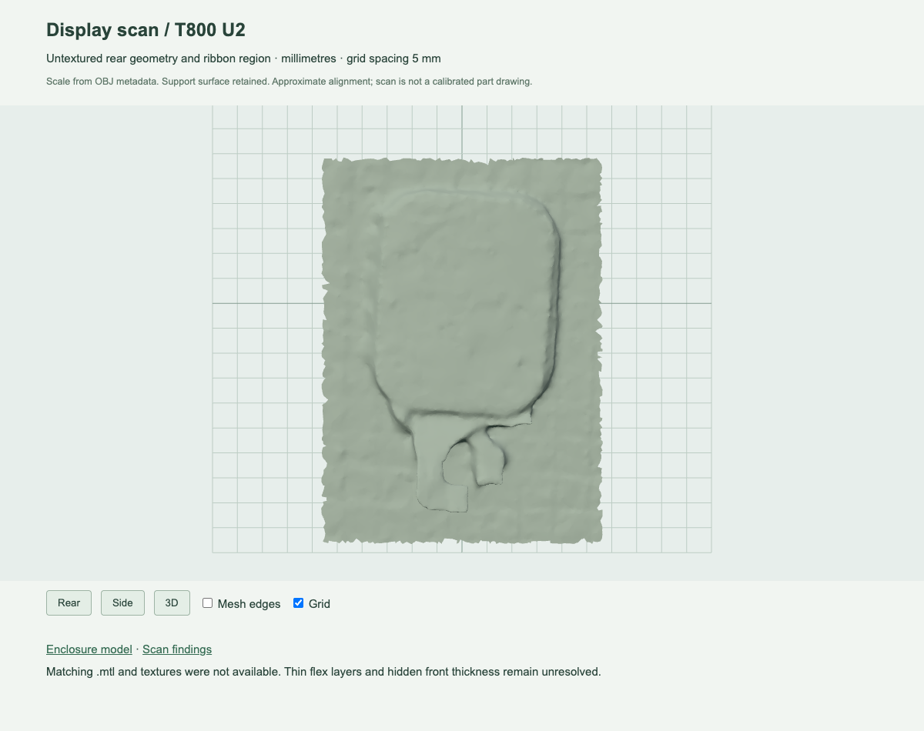
touchscreen_metal/scan_preview_check.png
