tunasafa/mp3-player-enclosure/touchscreen_metal/designs/T03_metal/display_carrier.step

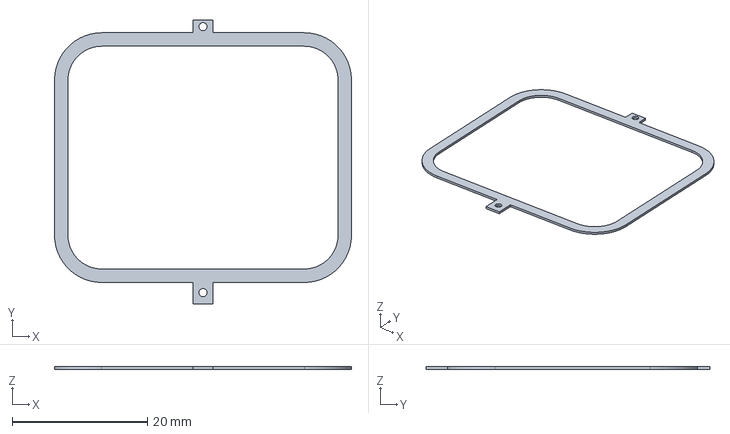
[picture p63: CAD file, 2026-09-12]
touchscreen_metal/designs/T03_metal/display_carrier.step
44.0 x 42.1 x 0.4 mm
