tunasafa/mp3-player-enclosure/touchscreen_metal/designs/T03_metal/reference_only/midframe.stl

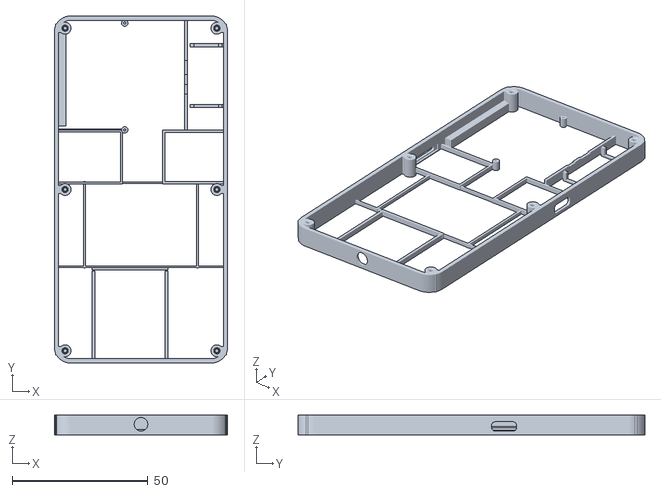
[picture p64: CAD file, 2026-09-12]
touchscreen_metal/designs/T03_metal/reference_only/midframe.stl
64.0 x 128.0 x 7.20
