tunasafa/mp3-player-enclosure/revision_04/designs/P04_compact/front_bezel.step

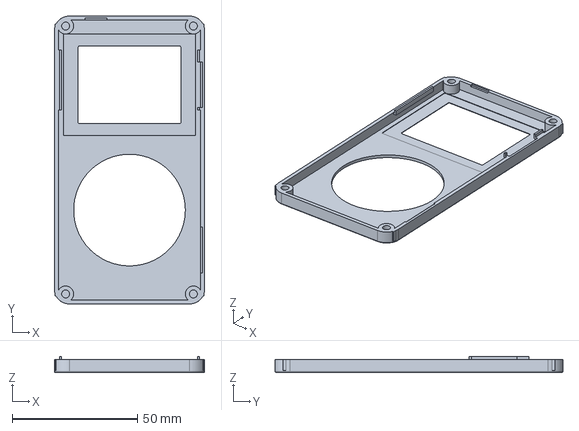
[picture p65: CAD file, 2026-09-12]
revision_04/designs/P04_compact/front_bezel.step
60.0 x 115.0 x 6.40 mm
