tunasafa/mp3-player-enclosure/revision_04/designs/P04_compact/reference_only/adafruit_6309_placed_VENDOR.step

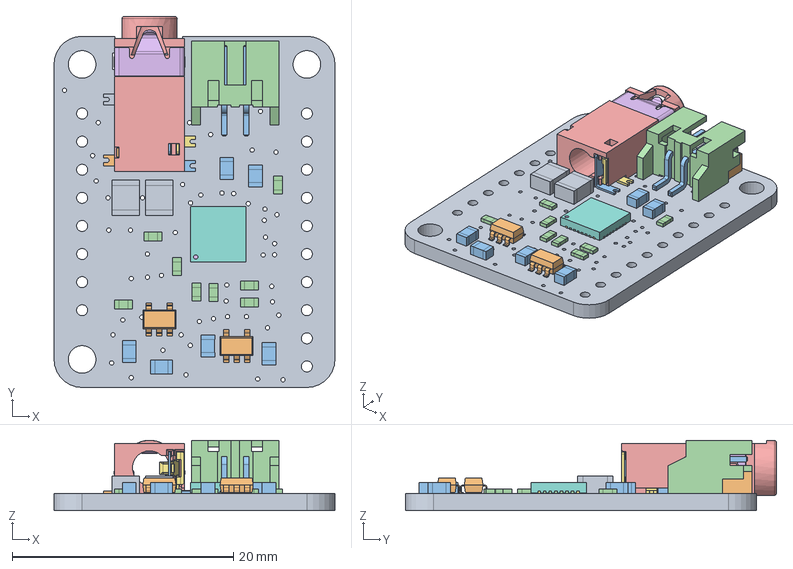
[picture p66: CAD file, 2026-09-12]
revision_04/designs/P04_compact/reference_only/adafruit_6309_placed_VENDOR.step
25.4 x 33.5 x 6.37 mm
