tunasafa/mp3-player-enclosure/revision_04/studies/dac_orientation/flipped_REFERENCE_ONLY.step

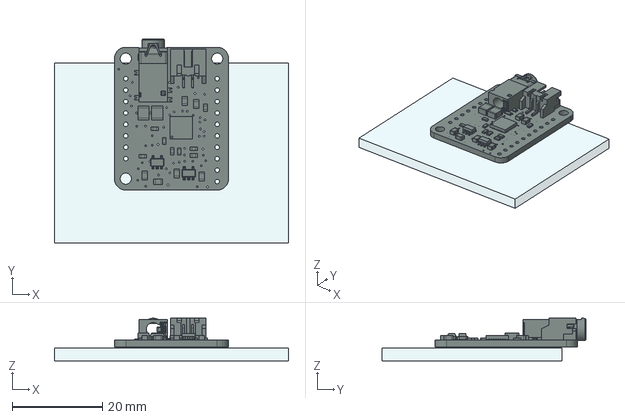
[picture p67: CAD file, 2026-09-11]
revision_04/studies/dac_orientation/flipped_REFERENCE_ONLY.step
52.0 x 45.2 x 9.47 mm
unaltered_vendor_DAC
assumed_LCD
