tunasafa/mp3-player-enclosure/revision_04/studies/detached_jack/reference_only/sj_3523_placed_DRAWING.step

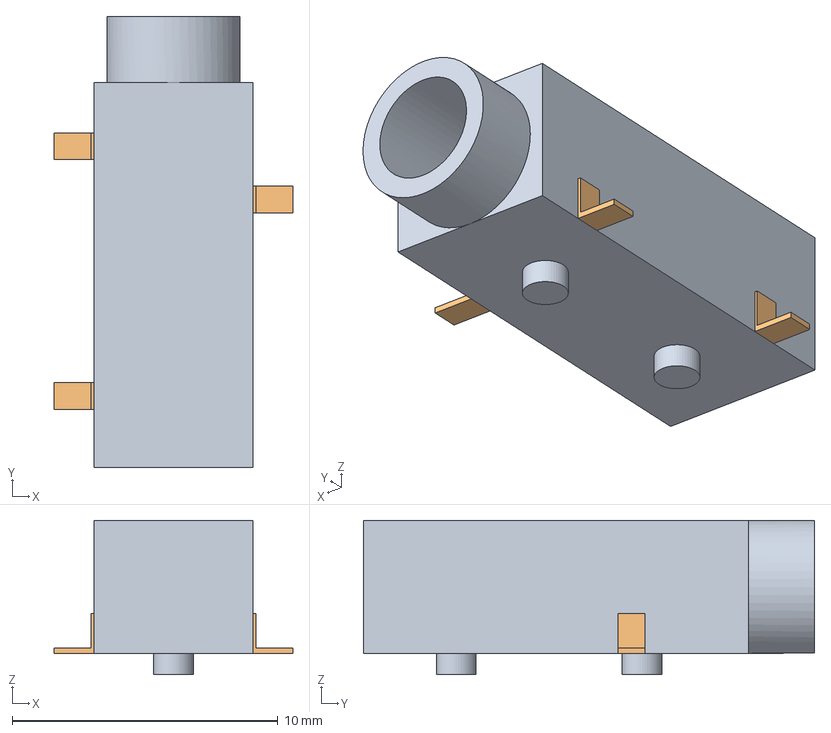
[picture p68: CAD file, 2026-09-12]
revision_04/studies/detached_jack/reference_only/sj_3523_placed_DRAWING.step
9.00 x 17.0 x 5.80 mm
