tunasafa/mp3-player-enclosure/touchscreen_01/designs/T01_concept/STL/battery_tray_FIT_CONCEPT.stl

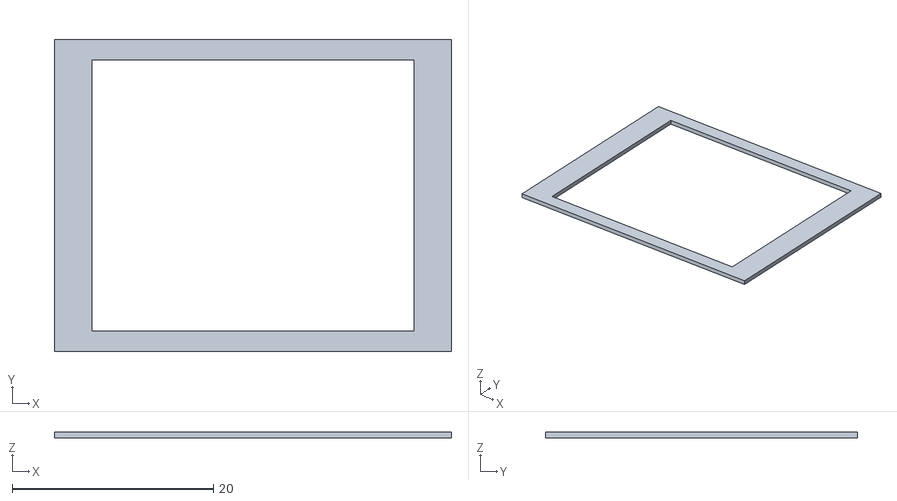
[picture p69: CAD file, 2026-09-12]
touchscreen_01/designs/T01_concept/STL/battery_tray_FIT_CONCEPT.stl
39.5 x 31.0 x 0.6
