tunasafa/mp3-player-enclosure/touchscreen_01/designs/T02_bottom_jack/STL/rear_shell_FIT_PROTOTYPE.stl

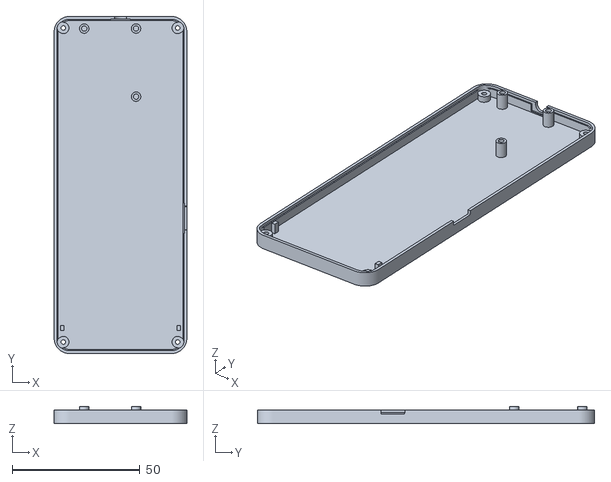
[picture p70: CAD file, 2026-09-12]
touchscreen_01/designs/T02_bottom_jack/STL/rear_shell_FIT_PROTOTYPE.stl
52.0 x 132.0 x 6.83
