tunasafa/mp3-player-enclosure/touchscreen_02/pla_fit/parts/carrier.step

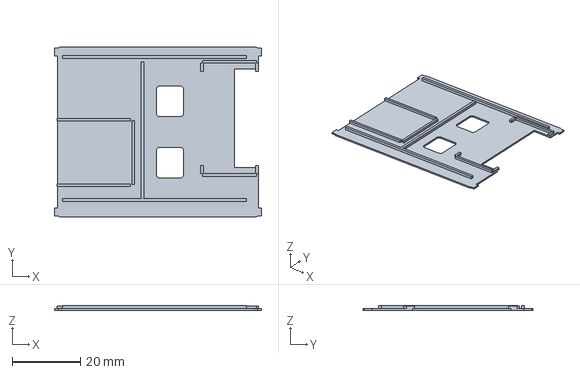
[picture p71: CAD file, 2026-09-30]
touchscreen_02/pla_fit/parts/carrier.step
60.8 x 50.0 x 1.40 mm
