tunasafa/mp3-player-enclosure/touchscreen_metal/designs/T03_metal/front_bezel.step

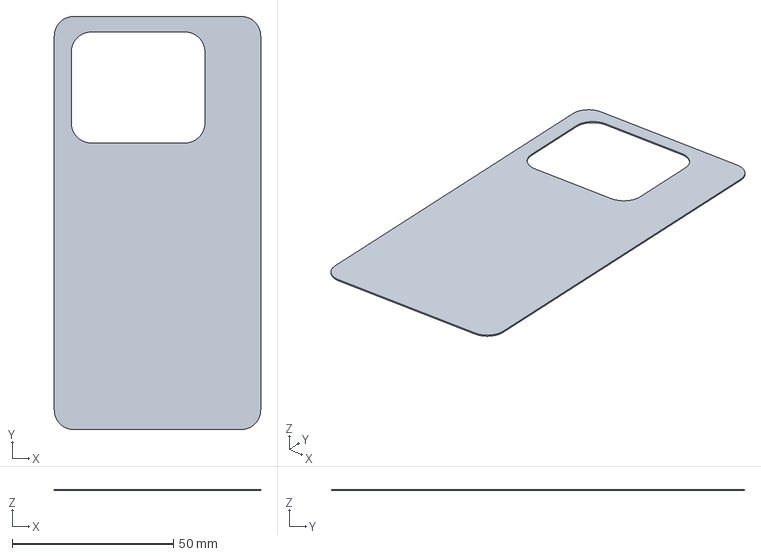
[picture p72: CAD file, 2026-09-12]
touchscreen_metal/designs/T03_metal/front_bezel.step
64.0 x 128.0 x 0.4 mm
