tunasafa/mp3-player-enclosure/touchscreen_metal/designs/T03_metal/reference_only/battery_foam.stl

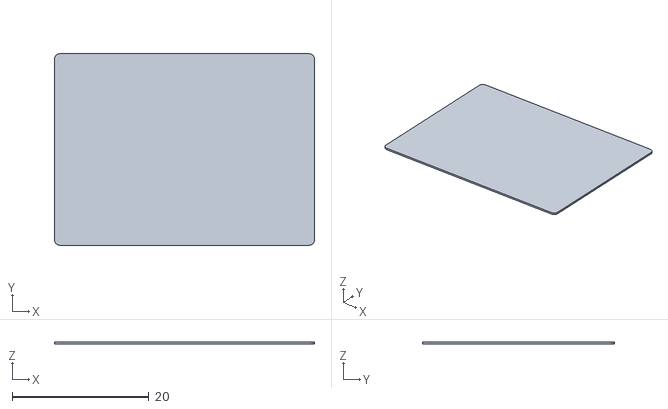
[picture p73: CAD file, 2026-09-12]
touchscreen_metal/designs/T03_metal/reference_only/battery_foam.stl
38.0 x 28.0 x 0.3
