tunasafa/mp3-player-enclosure/revision_04/designs/P04_compact/rear_shell.step

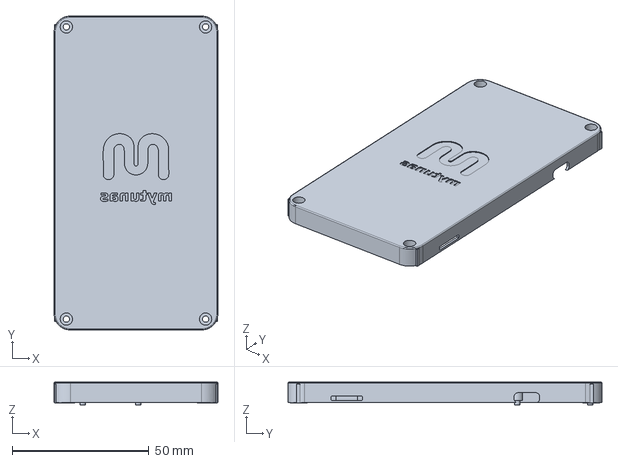
[picture p74: CAD file, 2026-09-12]
revision_04/designs/P04_compact/rear_shell.step
60.0 x 115.0 x 8.40 mm
