tunasafa/mp3-player-enclosure/revision_04/designs/P04_compact/reference_only/xiao.stl

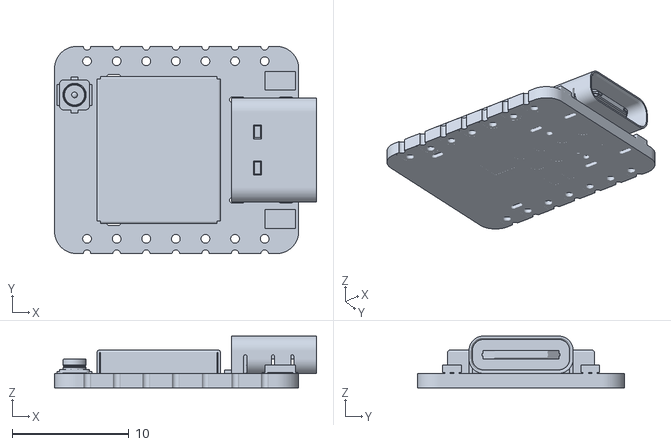
[picture p75: CAD file, 2026-09-11]
revision_04/designs/P04_compact/reference_only/xiao.stl
22.5 x 17.8 x 4.46
