tunasafa/mp3-player-enclosure/touchscreen_01/designs/T01_concept/rear_shell.step

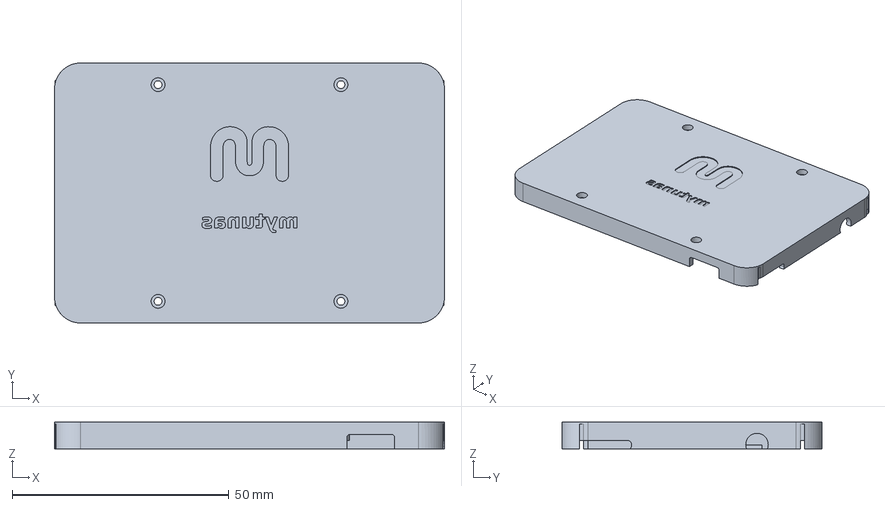
[picture p76: CAD file, 2026-09-12]
touchscreen_01/designs/T01_concept/rear_shell.step
90.0 x 60.0 x 6.20 mm
