tunasafa/mp3-player-enclosure/touchscreen_01/designs/T02_bottom_jack/STL/front_bezel_FIT_PROTOTYPE.stl

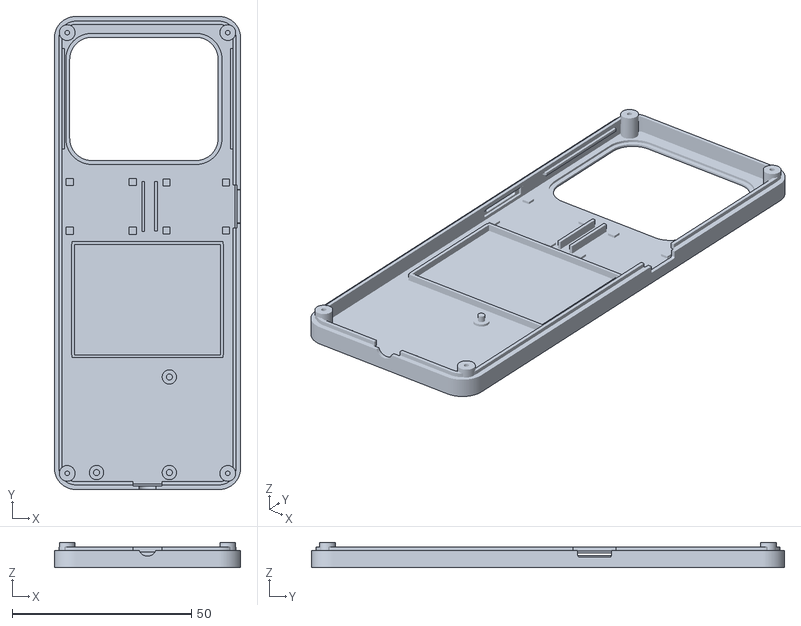
[picture p77: CAD file, 2026-09-12]
touchscreen_01/designs/T02_bottom_jack/STL/front_bezel_FIT_PROTOTYPE.stl
52.0 x 132.0 x 7.00
