tunasafa/mp3-player-enclosure/touchscreen_02/pla_fit/parts/rear_lid.step

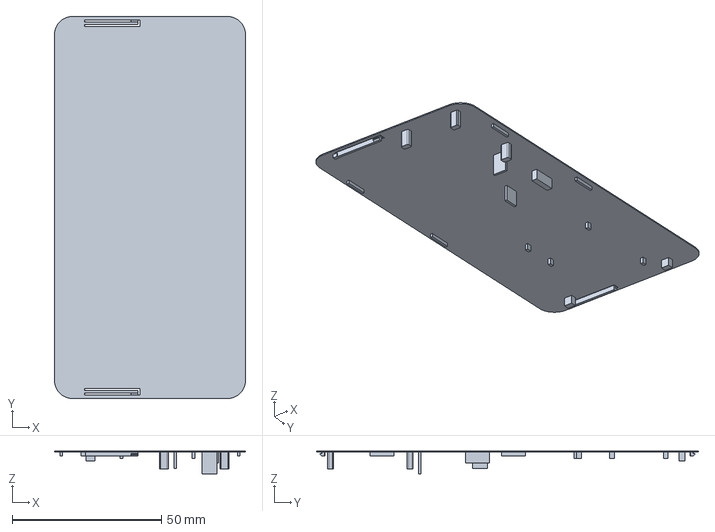
[picture p78: CAD file, 2026-09-30]
touchscreen_02/pla_fit/parts/rear_lid.step
64.0 x 128.0 x 7.70 mm
