tunasafa/mp3-player-enclosure/revision_04/designs/P04_compact/clear_lens_0p6_REFERENCE.dxf

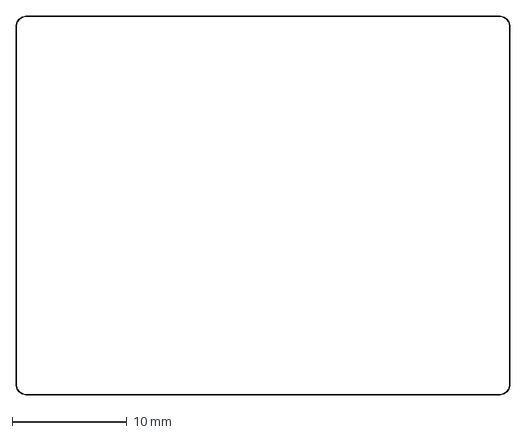
[picture p79: CAD file, 2026-09-12]
revision_04/designs/P04_compact/clear_lens_0p6_REFERENCE.dxf
43.0 x 33.0 mm
