tunasafa/mp3-player-enclosure/touchscreen_01/designs/T01_concept/battery_tray.step

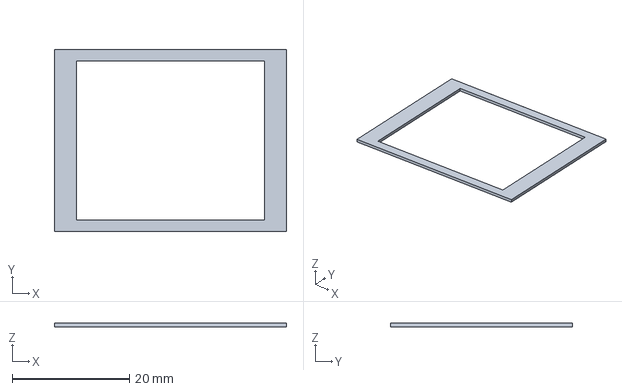
[picture p80: CAD file, 2026-09-12]
touchscreen_01/designs/T01_concept/battery_tray.step
39.5 x 31.0 x 0.6 mm
