tunasafa/mp3-player-enclosure/touchscreen_02/pla_fit/parts/coupon_receiver.step

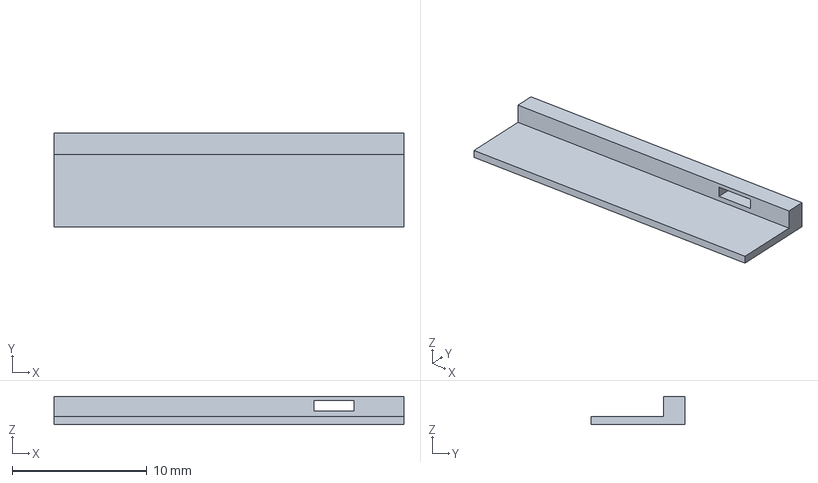
[picture p81: CAD file, 2026-09-30]
touchscreen_02/pla_fit/parts/coupon_receiver.step
26.0 x 7.00 x 2.10 mm
