tunasafa/mp3-player-enclosure/touchscreen_metal/designs/T03_metal/reference_only/rear_shell.stl

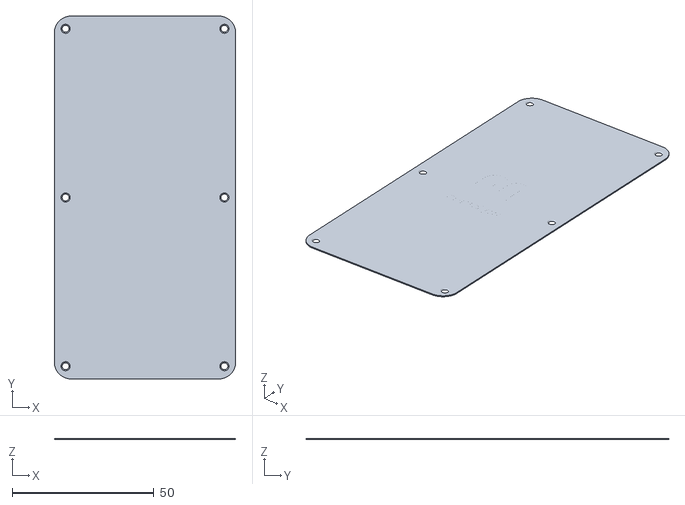
[picture p82: CAD file, 2026-09-12]
touchscreen_metal/designs/T03_metal/reference_only/rear_shell.stl
64.0 x 128.0 x 0.4
