tunasafa/mp3-player-enclosure/revision_04/designs/P04_compact/reference_only/fpc8.stl

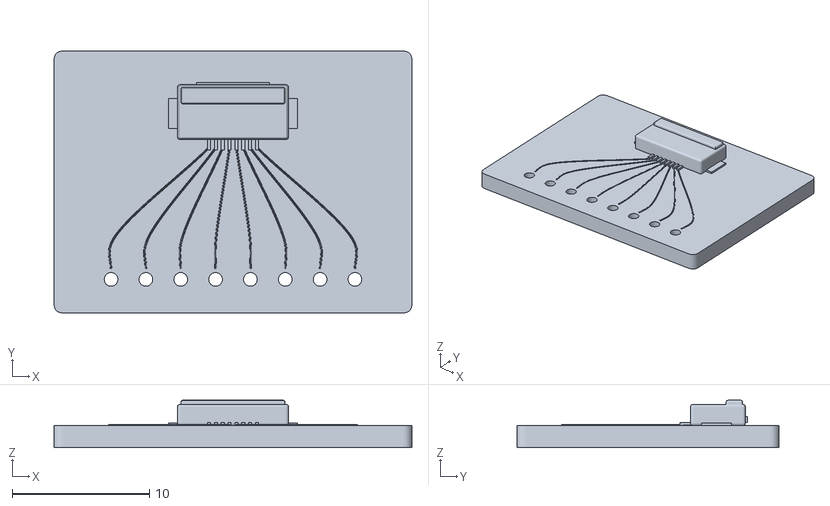
[picture p83: CAD file, 2026-09-11]
revision_04/designs/P04_compact/reference_only/fpc8.stl
26.1 x 19.1 x 3.46
