tunasafa/mp3-player-enclosure/touchscreen_02/pla_fit/parts/front_tray.step

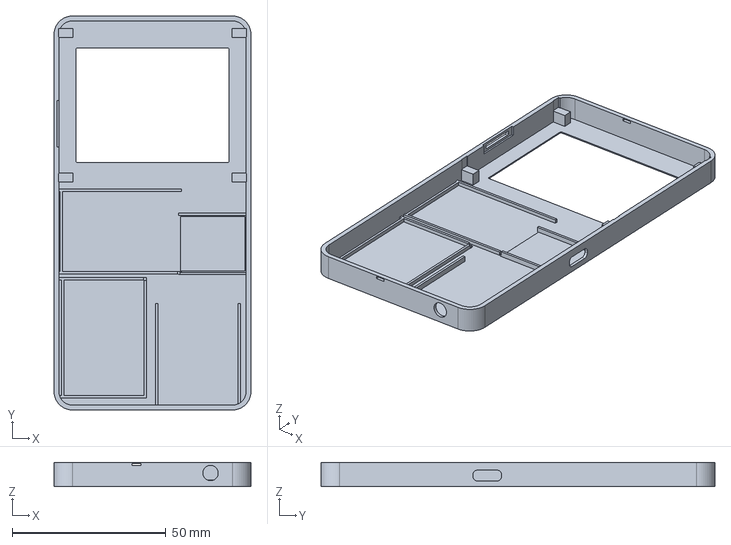
[picture p84: CAD file, 2026-09-30]
touchscreen_02/pla_fit/parts/front_tray.step
64.0 x 128.0 x 7.90 mm
