tunasafa/mp3-player-enclosure/touchscreen_metal/designs/T03_metal/reference_only/display_flex.stl

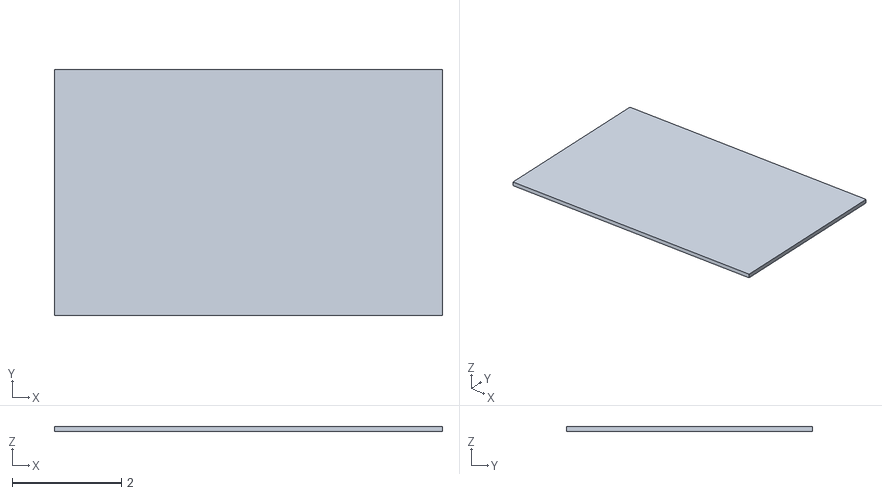
[picture p85: CAD file, 2026-09-12]
touchscreen_metal/designs/T03_metal/reference_only/display_flex.stl
7.10 x 4.50 x 0.1
