tunasafa/mp3-player-enclosure/revision_04/designs/P04_compact/reference_only/battery_envelope.stl

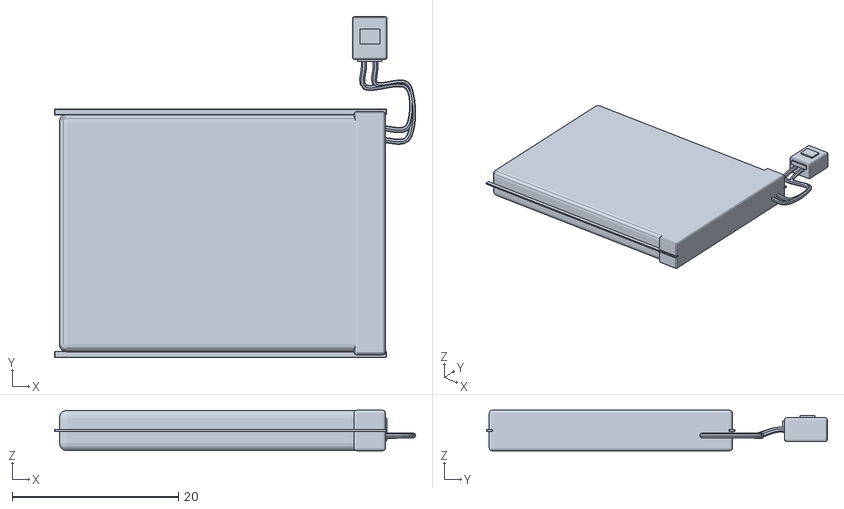
[picture p86: CAD file, 2026-09-11]
revision_04/designs/P04_compact/reference_only/battery_envelope.stl
43.5 x 41.1 x 4.90
