tunasafa/mp3-player-enclosure/touchscreen_02/pla_fit/parts/coupon_lid.step

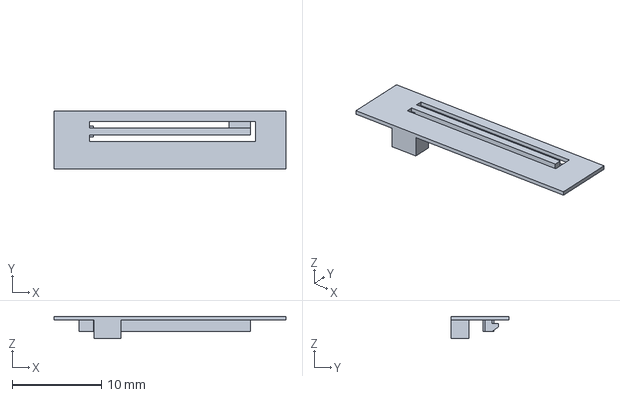
[picture p87: CAD file, 2026-09-30]
touchscreen_02/pla_fit/parts/coupon_lid.step
26.0 x 6.50 x 2.50 mm
