tunasafa/mp3-player-enclosure/touchscreen_metal/designs/T03_metal/rear_marking_ONLY.dxf

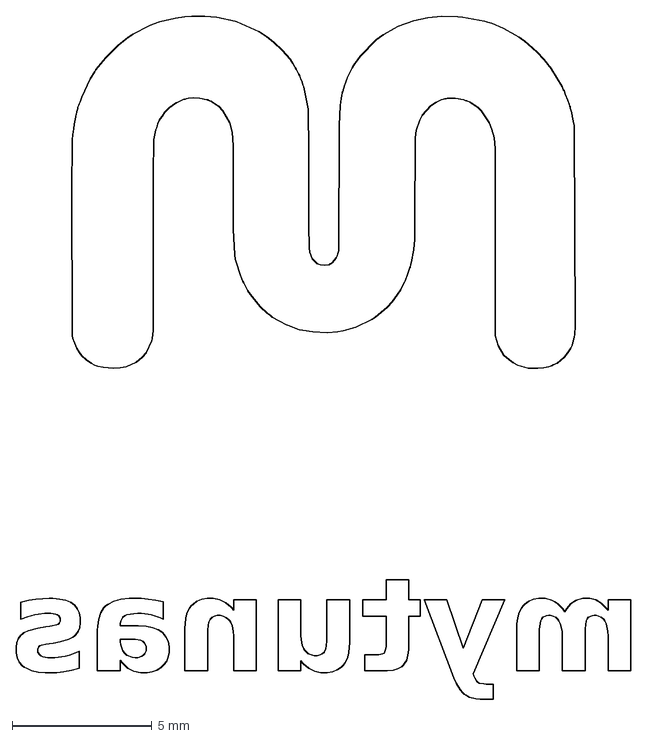
[picture p88: CAD file, 2026-09-12]
touchscreen_metal/designs/T03_metal/rear_marking_ONLY.dxf
22.0 x 24.4 mm
