tunasafa/mp3-player-enclosure/revision_04/designs/P04_compact/reference_only/clickwheel_envelope.stl

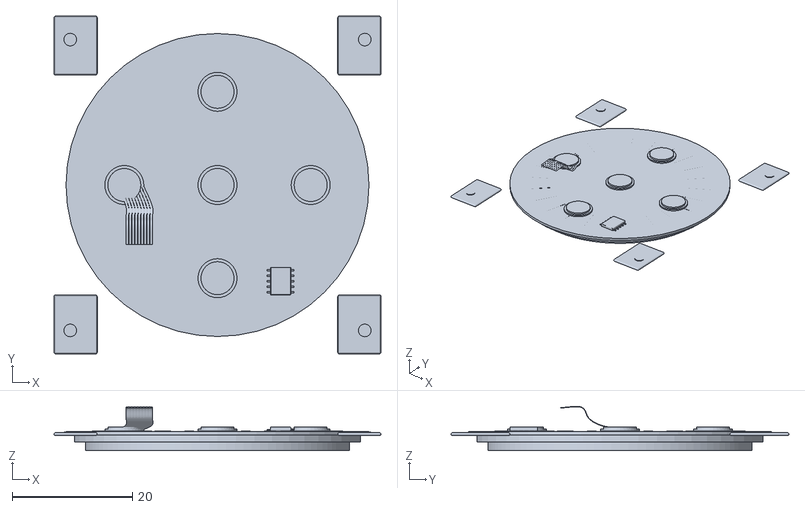
[picture p89: CAD file, 2026-09-11]
revision_04/designs/P04_compact/reference_only/clickwheel_envelope.stl
54.4 x 56.2 x 7.38
