tunasafa/mp3-player-enclosure/touchscreen_02/pla_fit/parts/KR3_REMADE_standard_6mmD_PROVISIONAL.stl

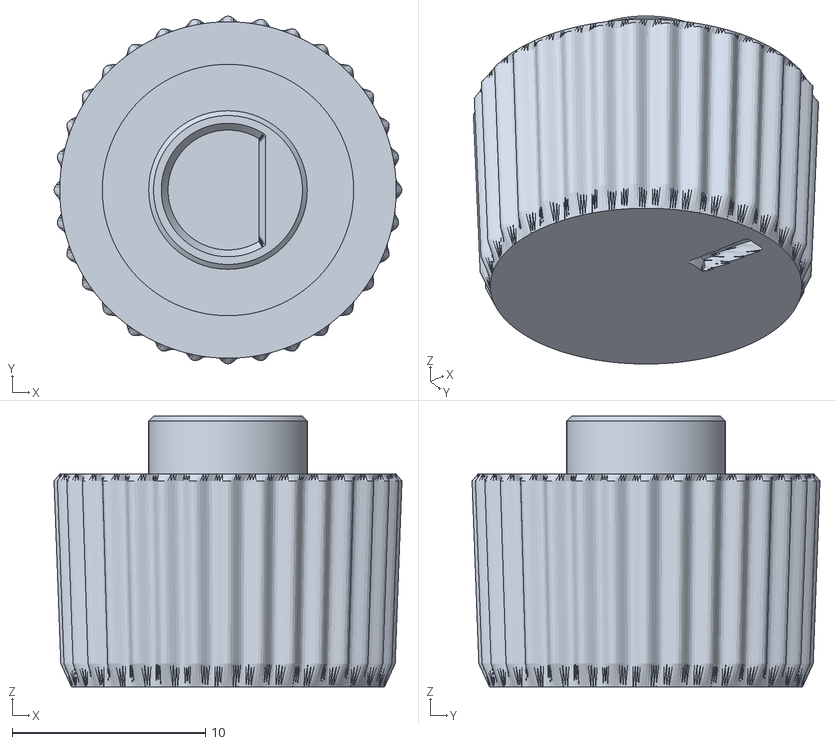
[picture p90: CAD file, 2026-09-30]
touchscreen_02/pla_fit/parts/KR3_REMADE_standard_6mmD_PROVISIONAL.stl
18.0 x 18.0 x 14.0
