tunasafa/mp3-player-enclosure/touchscreen_metal/designs/T03_metal/reference_only/touch_zif.stl

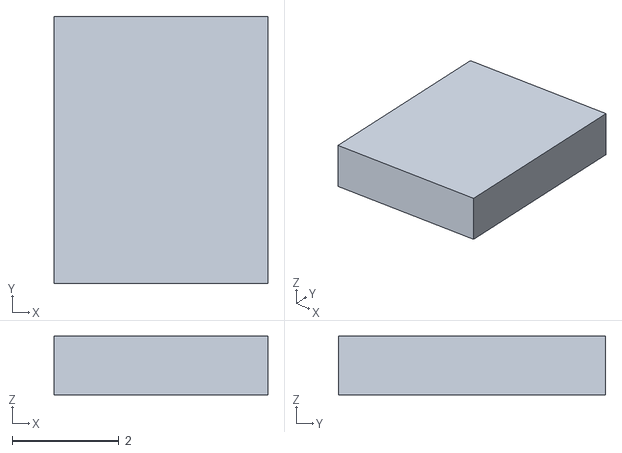
[picture p92: CAD file, 2026-09-12]
touchscreen_metal/designs/T03_metal/reference_only/touch_zif.stl
4.00 x 5.00 x 1.10
