tunasafa/mp3-player-enclosure/touchscreen_metal/designs/T03_metal/display_carrier_profile.dxf

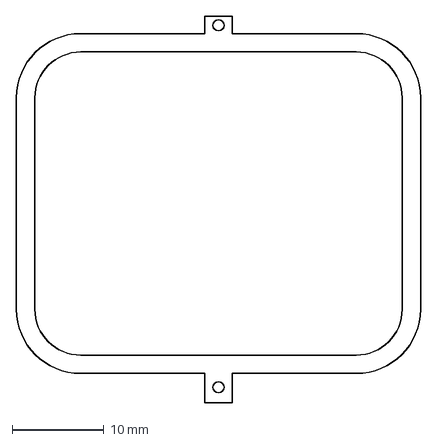
[picture p93: CAD file, 2026-09-12]
touchscreen_metal/designs/T03_metal/display_carrier_profile.dxf
44.0 x 42.1 mm
