tunasafa/mp3-player-enclosure/touchscreen_metal/designs/T03_metal/reference_only/touch_flex.stl

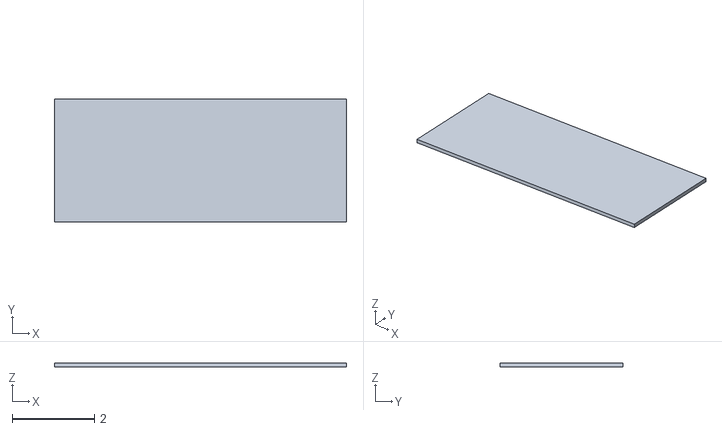
[picture p94: CAD file, 2026-09-12]
touchscreen_metal/designs/T03_metal/reference_only/touch_flex.stl
7.10 x 3.00 x 0.1
