tunasafa/mp3-player-enclosure/revision_04/designs/P04_compact/reference_only/microsd.stl

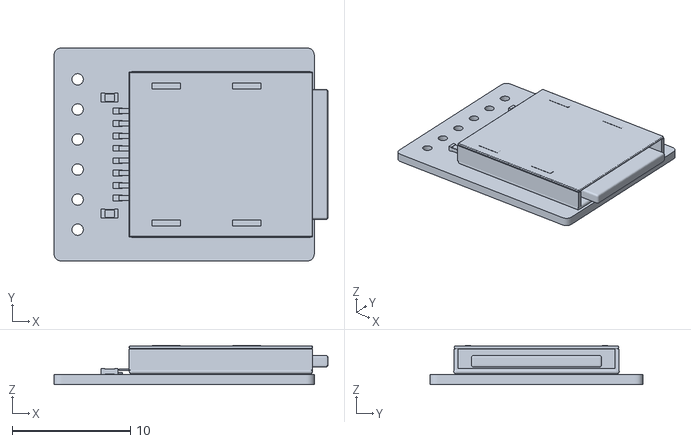
[picture p95: CAD file, 2026-09-11]
revision_04/designs/P04_compact/reference_only/microsd.stl
23.2 x 18.0 x 3.30
