tunasafa/mp3-player-enclosure/touchscreen_metal/designs/T03_metal/front_bezel_profile.dxf

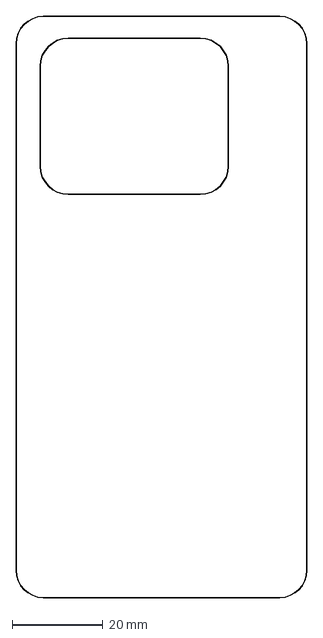
[picture p96: CAD file, 2026-09-12]
touchscreen_metal/designs/T03_metal/front_bezel_profile.dxf
64.0 x 128.0 mm
