tunasafa/mp3-player-enclosure/touchscreen_metal/designs/T03_metal/reference_only/microsd.stl

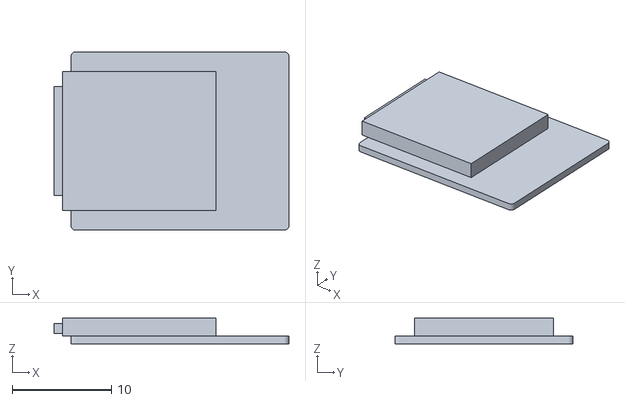
[picture p97: CAD file, 2026-09-12]
touchscreen_metal/designs/T03_metal/reference_only/microsd.stl
23.7 x 18.0 x 2.60
