tunasafa/mp3-player-enclosure/revision_04/designs/P04_compact/reference_only/display_envelope.stl

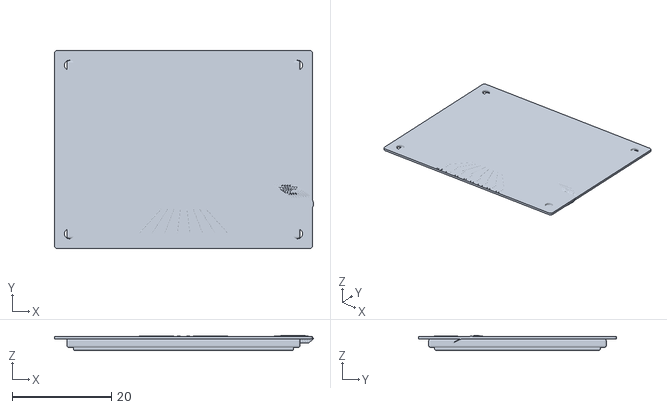
[picture p98: CAD file, 2026-09-11]
revision_04/designs/P04_compact/reference_only/display_envelope.stl
52.2 x 40.0 x 2.97
