tunasafa/mp3-player-enclosure/touchscreen_metal/designs/T03_metal/reference_only/touch_lcd_tape.stl

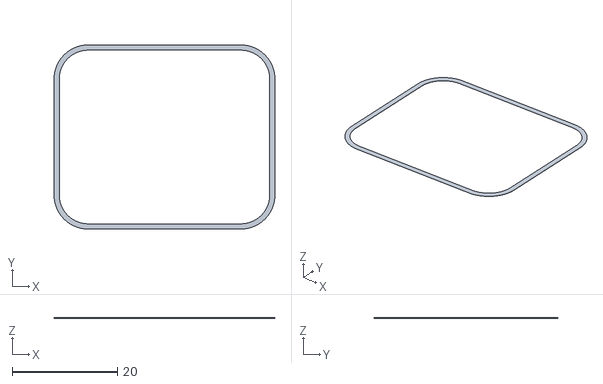
[picture p99: CAD file, 2026-09-12]
touchscreen_metal/designs/T03_metal/reference_only/touch_lcd_tape.stl
42.0 x 35.0 x 0.2
