tunasafa/mp3-player-enclosure/revision_04/designs/P04_compact/reference_only/clear_lens_reference.stl

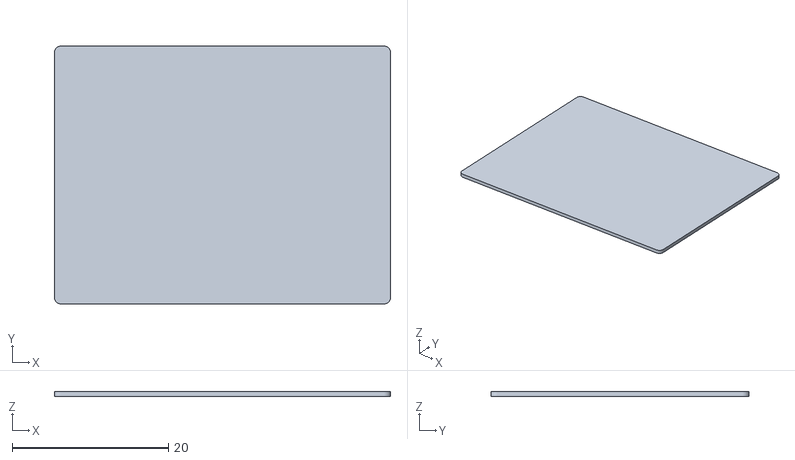
[picture p100: CAD file, 2026-09-11]
revision_04/designs/P04_compact/reference_only/clear_lens_reference.stl
43.0 x 33.0 x 0.6
