tunasafa/mp3-player-enclosure/touchscreen_metal/designs/T03_metal/reference_only/control.stl

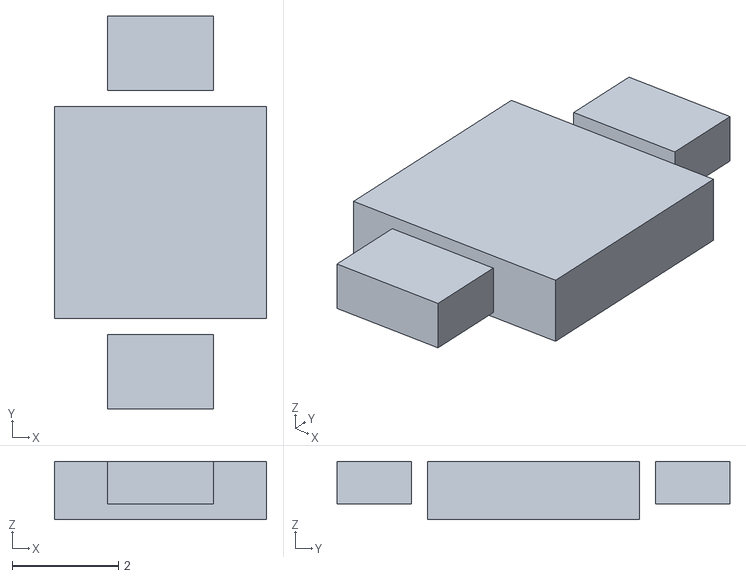
[picture p102: CAD file, 2026-09-12]
touchscreen_metal/designs/T03_metal/reference_only/control.stl
4.00 x 7.40 x 1.10
