tunasafa/mp3-player-enclosure/touchscreen_metal/designs/T03_metal/reference_only/battery.stl

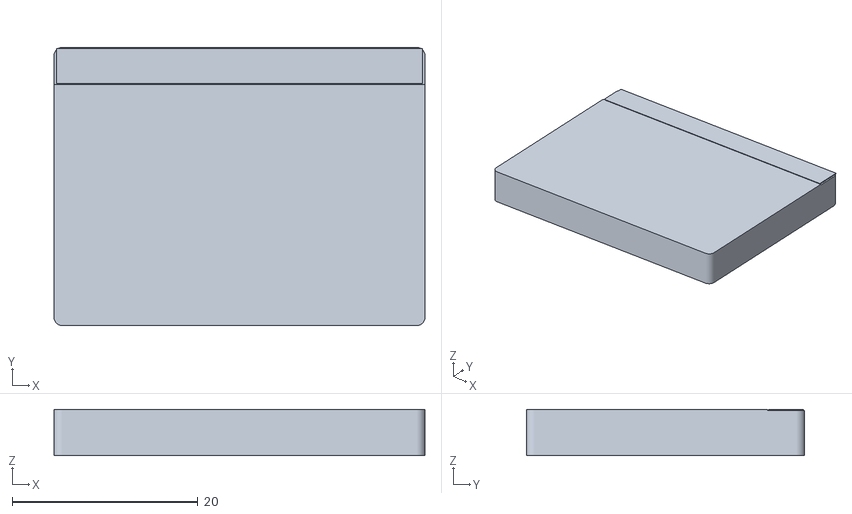
[picture p103: CAD file, 2026-09-12]
touchscreen_metal/designs/T03_metal/reference_only/battery.stl
40.0 x 30.0 x 5.00
