tunasafa/mp3-player-enclosure/touchscreen_metal/designs/T03_metal/reference_only/dac_retention.stl

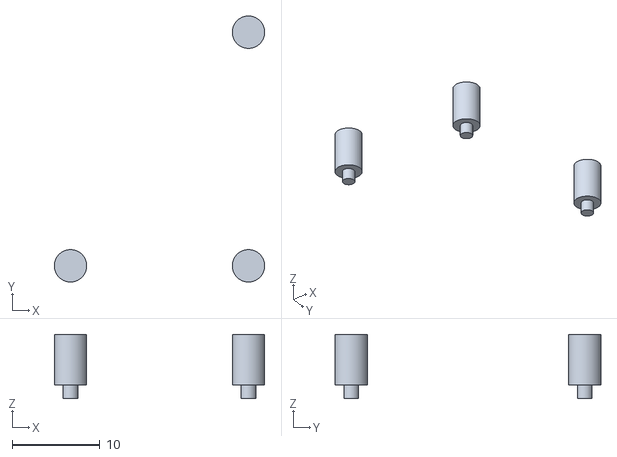
[picture p105: CAD file, 2026-09-12]
touchscreen_metal/designs/T03_metal/reference_only/dac_retention.stl
24.0 x 30.4 x 7.35
