tunasafa/mp3-player-enclosure/touchscreen_metal/designs/T03_metal/reference_only/audio_insulator.stl

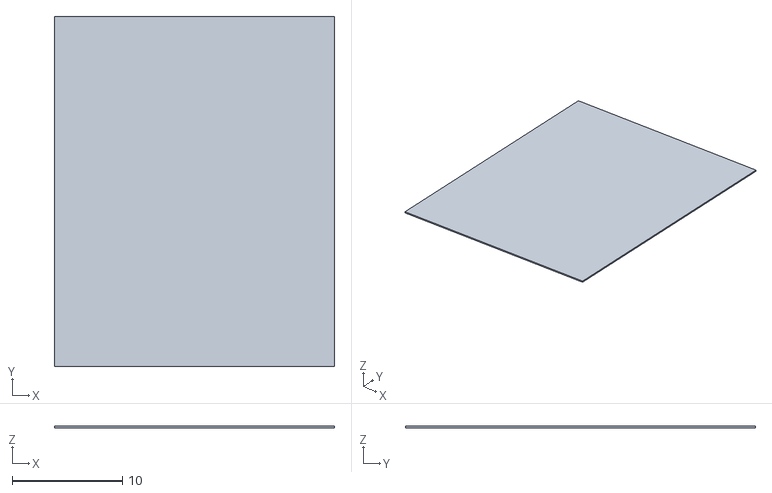
[picture p106: CAD file, 2026-09-12]
touchscreen_metal/designs/T03_metal/reference_only/audio_insulator.stl
25.4 x 31.8 x 0.15
