tunasafa/mp3-player-enclosure/touchscreen_metal/designs/T03_metal/reference_only/rear_liner.stl

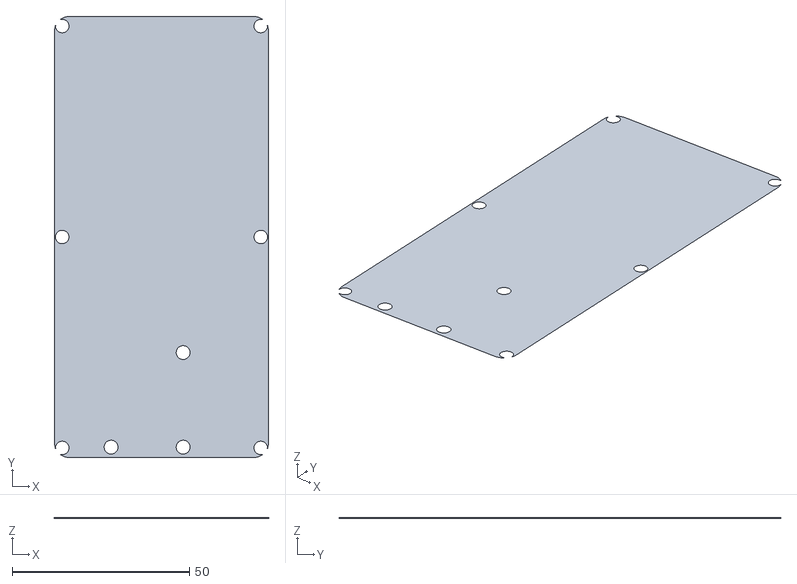
[picture p107: CAD file, 2026-09-12]
touchscreen_metal/designs/T03_metal/reference_only/rear_liner.stl
60.4 x 124.4 x 0.07
