tunasafa/mp3-player-enclosure/touchscreen_metal/designs/T03_metal/reference_only/touch_sensor.stl

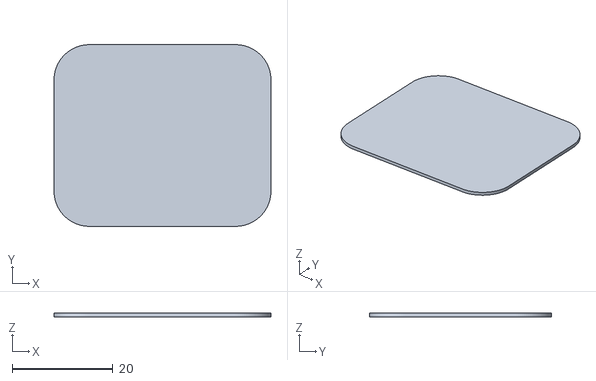
[picture p109: CAD file, 2026-09-12]
touchscreen_metal/designs/T03_metal/reference_only/touch_sensor.stl
43.0 x 36.0 x 0.7
