tunasafa/mp3-player-enclosure/touchscreen_metal/designs/T03_metal/reference_only/xiao_insulator.stl

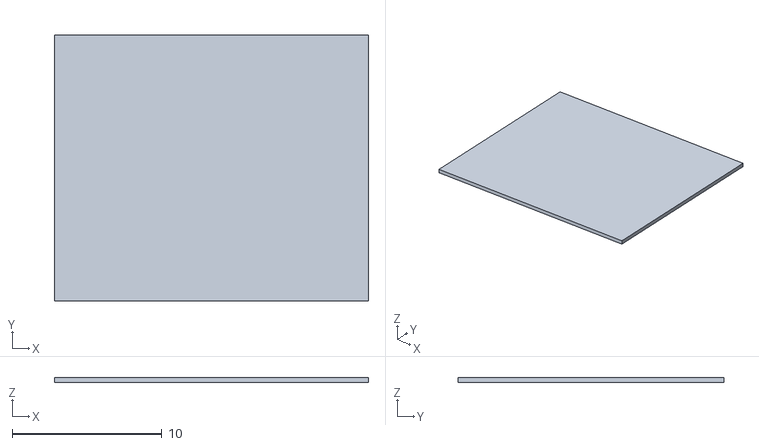
[picture p110: CAD file, 2026-09-12]
touchscreen_metal/designs/T03_metal/reference_only/xiao_insulator.stl
21.0 x 17.8 x 0.35
