tunasafa/mp3-player-enclosure/touchscreen_metal/designs/T03_metal/reference_only/interface_pcb.stl

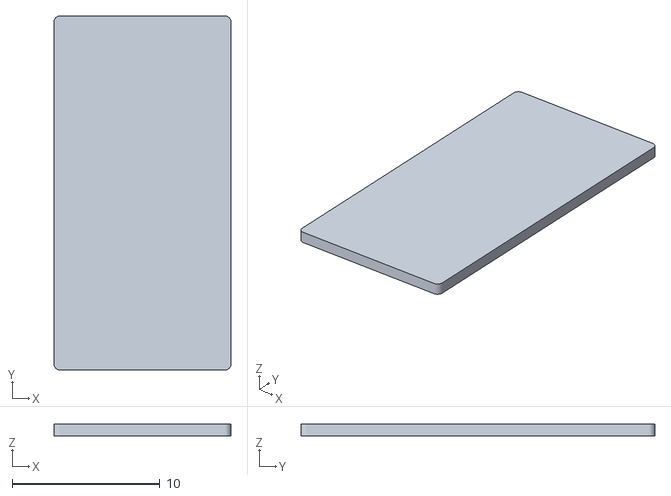
[picture p111: CAD file, 2026-09-12]
touchscreen_metal/designs/T03_metal/reference_only/interface_pcb.stl
12.0 x 24.0 x 0.8
