tunasafa/mp3-player-enclosure/touchscreen_metal/designs/T03_metal/reference_only/microsd_insulator.stl

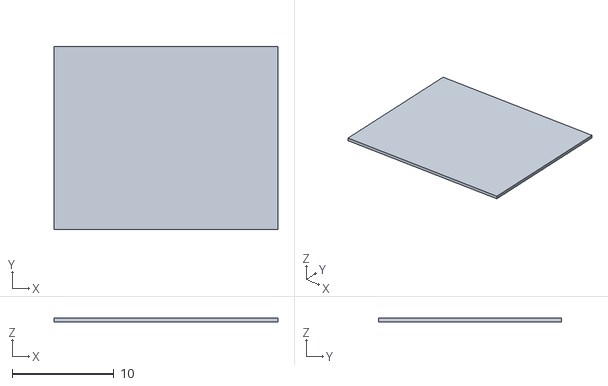
[picture p113: CAD file, 2026-09-12]
touchscreen_metal/designs/T03_metal/reference_only/microsd_insulator.stl
22.0 x 18.0 x 0.35
