tunasafa/mp3-player-enclosure/touchscreen_metal/designs/T03_metal/reference_only/lcd.stl

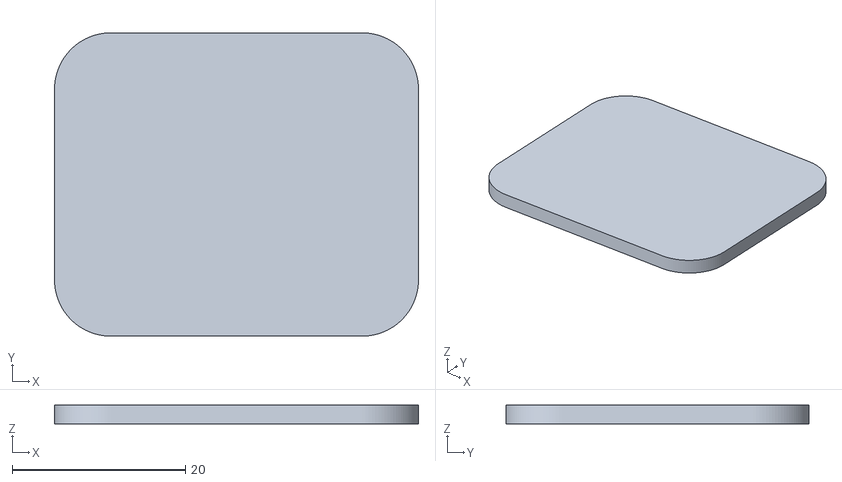
[picture p114: CAD file, 2026-09-12]
touchscreen_metal/designs/T03_metal/reference_only/lcd.stl
42.0 x 35.0 x 2.15
